Tinamous/ReallySmartBox/Images/2017-08-14 11.56.22.jpg

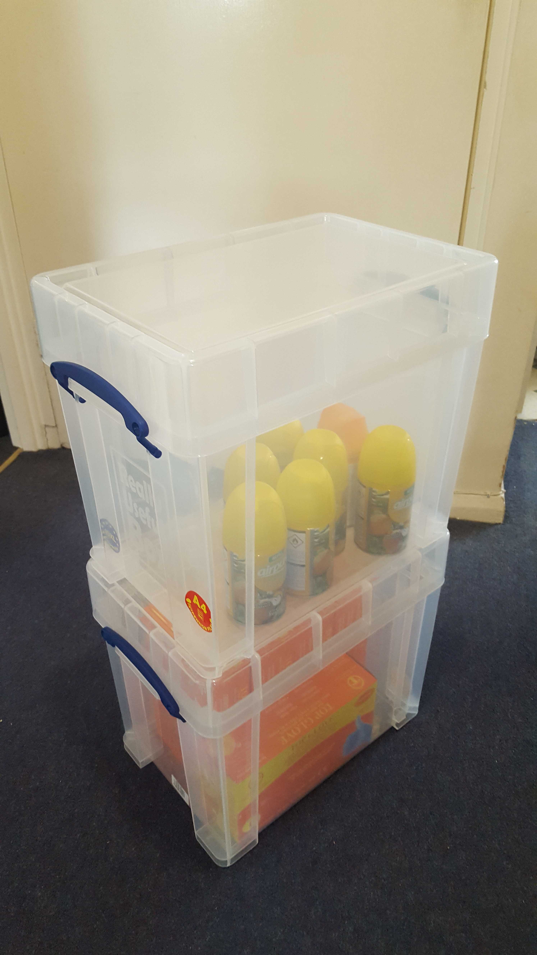
Images/2017-08-14 11.56.22.jpg
