Tinamous/ReallySmartBox/Images/2017-08-14 11.56.32.jpg

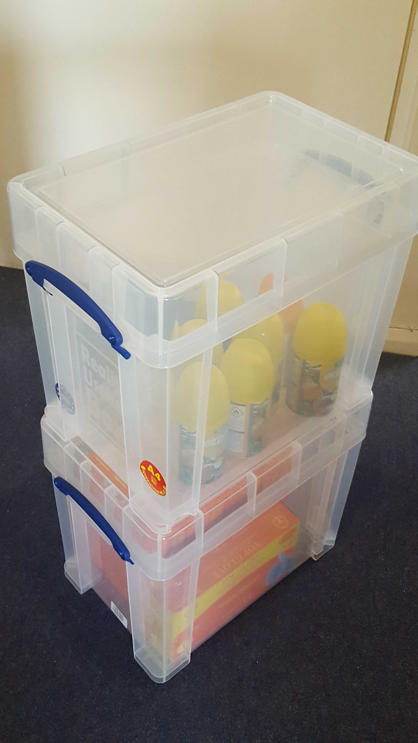
Images/2017-08-14 11.56.32.jpg
