Tinamous/ReallySmartBox/Images/2017-08-14 11.58.28.jpg

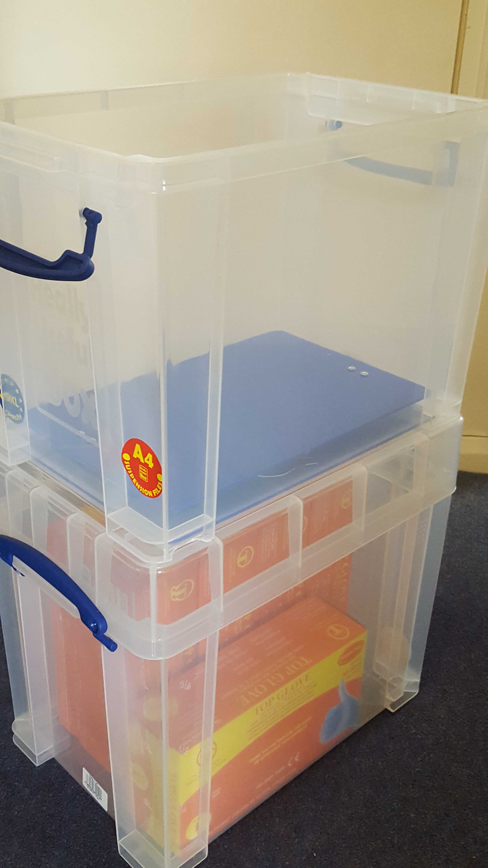
Images/2017-08-14 11.58.28.jpg
