Tinamous/ReallySmartBox/Images/2017-08-14 11.59.04.jpg

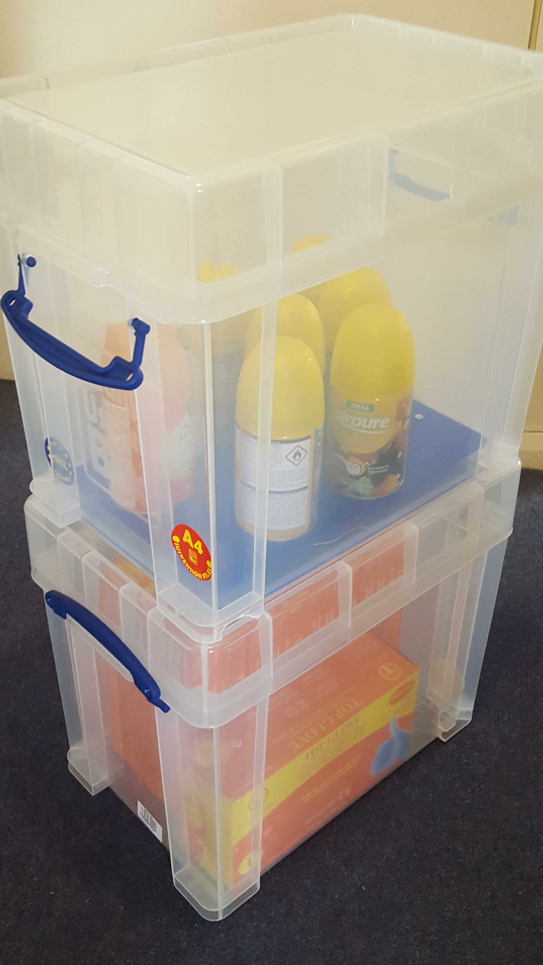
Images/2017-08-14 11.59.04.jpg
