Tinamous/ReallySmartBox/Images/2017-08-14 12.00.39.jpg

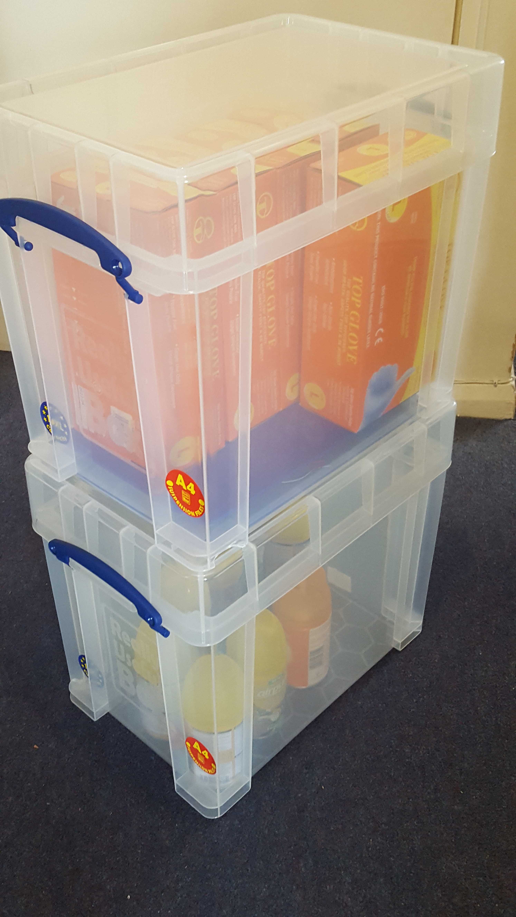
Images/2017-08-14 12.00.39.jpg
