Tinamous/ReallySmartBox/Images/2017-08-14 12.01.01.jpg

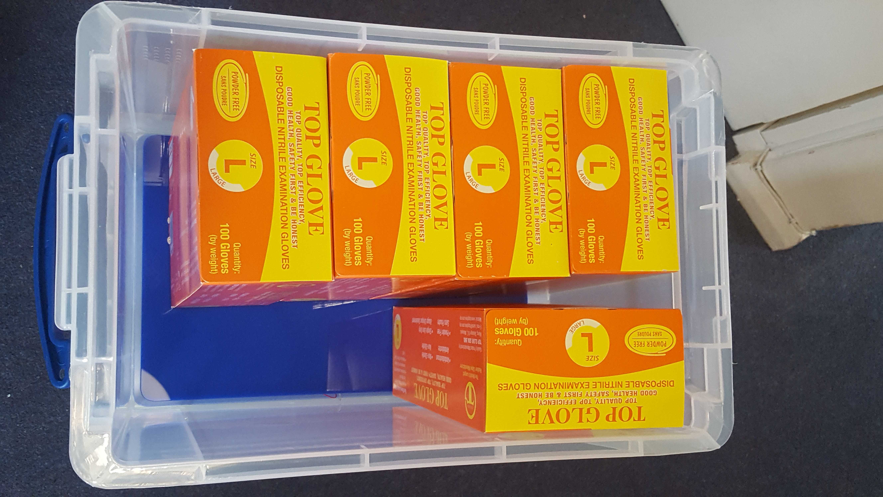
Images/2017-08-14 12.01.01.jpg
