Tinamous/ReallySmartBox/Images/2017-08-14 13.37.10.jpg

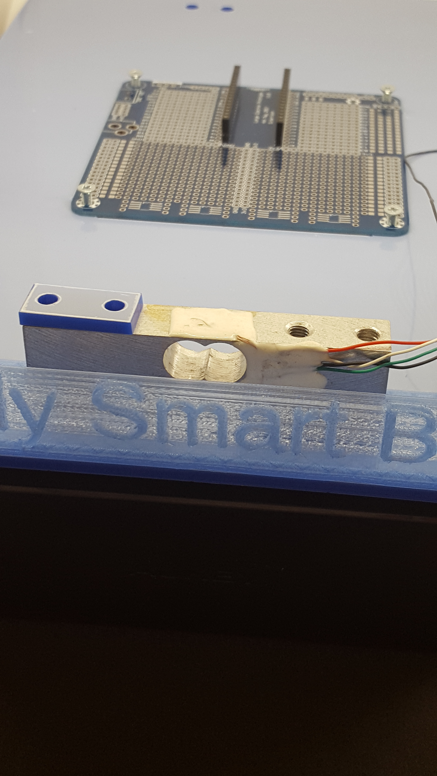
Images/2017-08-14 13.37.10.jpg
