Tinamous/ReallySmartBox/Images/2017-08-14 13.40.55.jpg

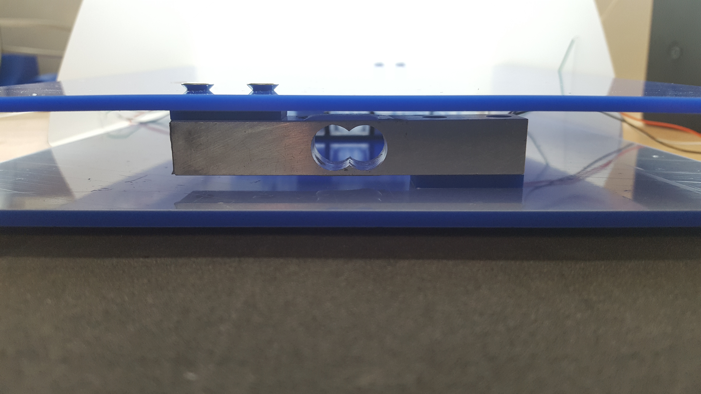
Images/2017-08-14 13.40.55.jpg
