Tinamous/ReallySmartBox/Images/2017-08-14 13.41.03.jpg

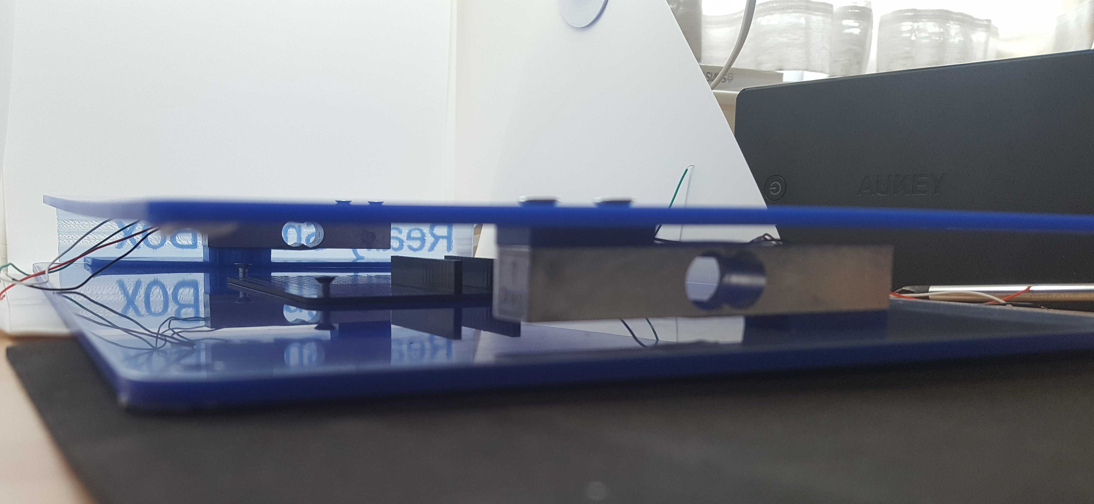
Images/2017-08-14 13.41.03.jpg
