Tinamous/ReallySmartBox/Images/2017-11-07 12.58.53.jpg

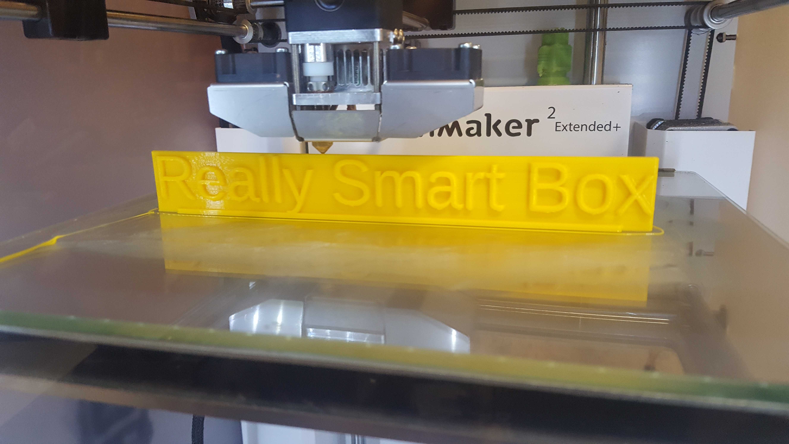
Images/2017-11-07 12.58.53.jpg
