Tinamous/ReallySmartBox/Images/2017-11-07 18.37.57.jpg

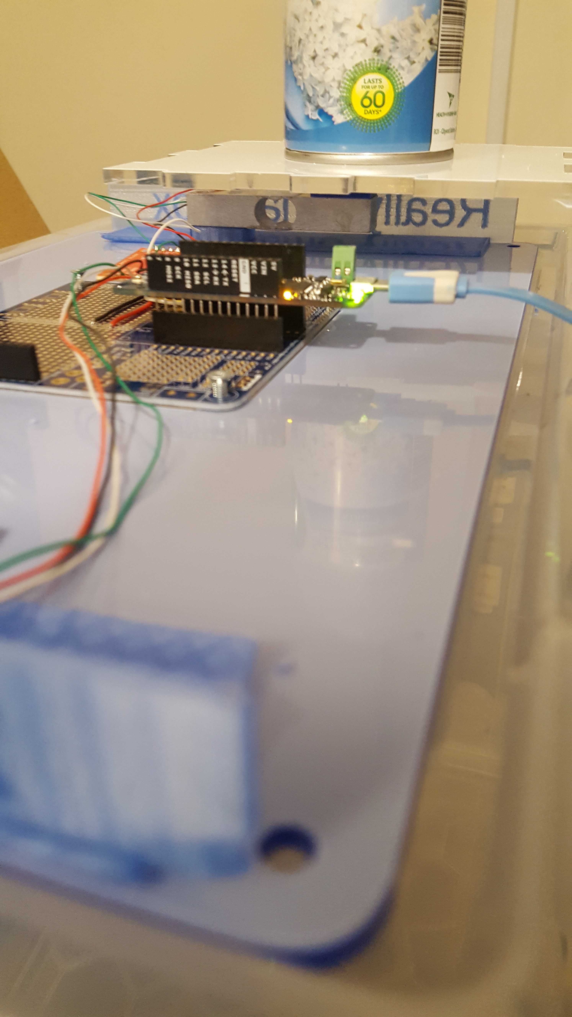
Images/2017-11-07 18.37.57.jpg
