Tinamous/ReallySmartBox/Images/2017-11-07 18.38.00.jpg

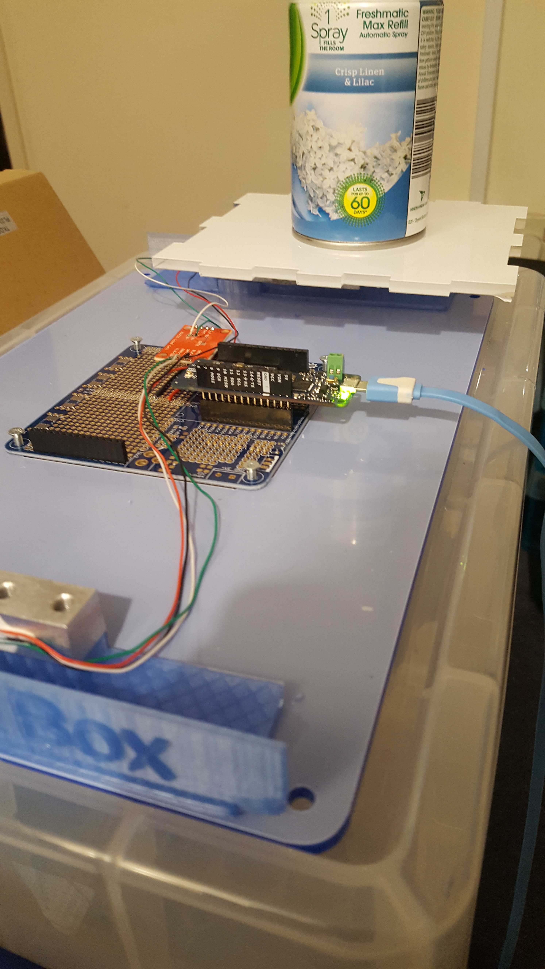
Images/2017-11-07 18.38.00.jpg
