Tinamous/ReallySmartBox/Images/2017-11-08 00.15.52.jpg

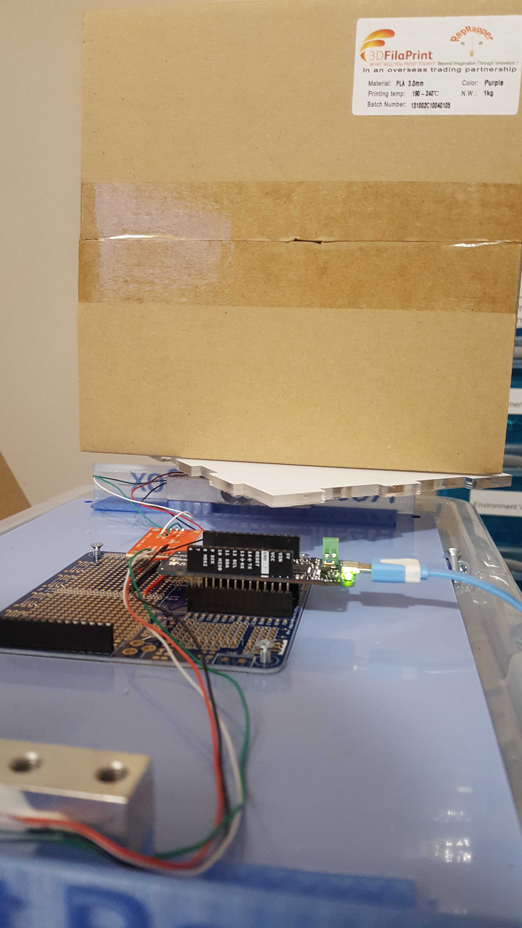
Images/2017-11-08 00.15.52.jpg
