Tinamous/ReallySmartBox/Images/2017-11-08 05.06.58.jpg

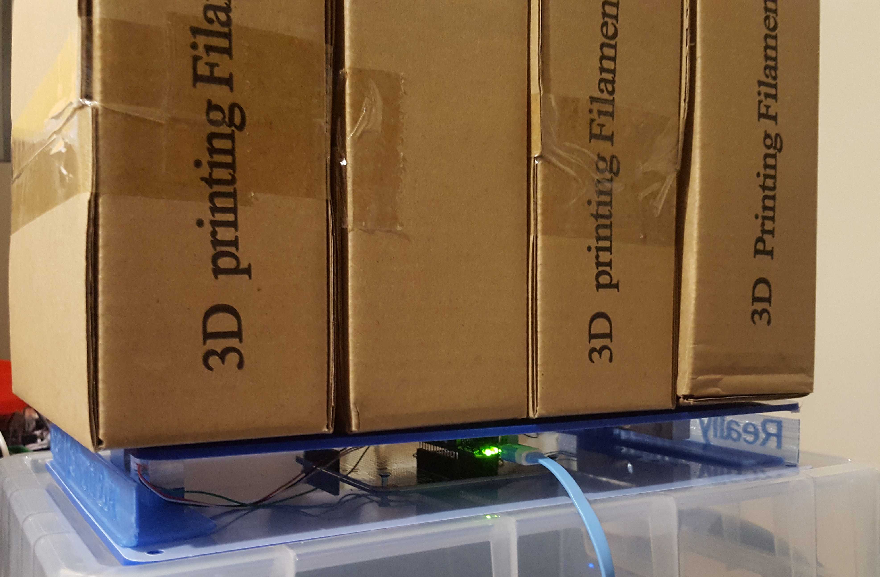
Images/2017-11-08 05.06.58.jpg
