Tinamous/ReallySmartBox/Images/2017-11-09 22.32.21.jpg

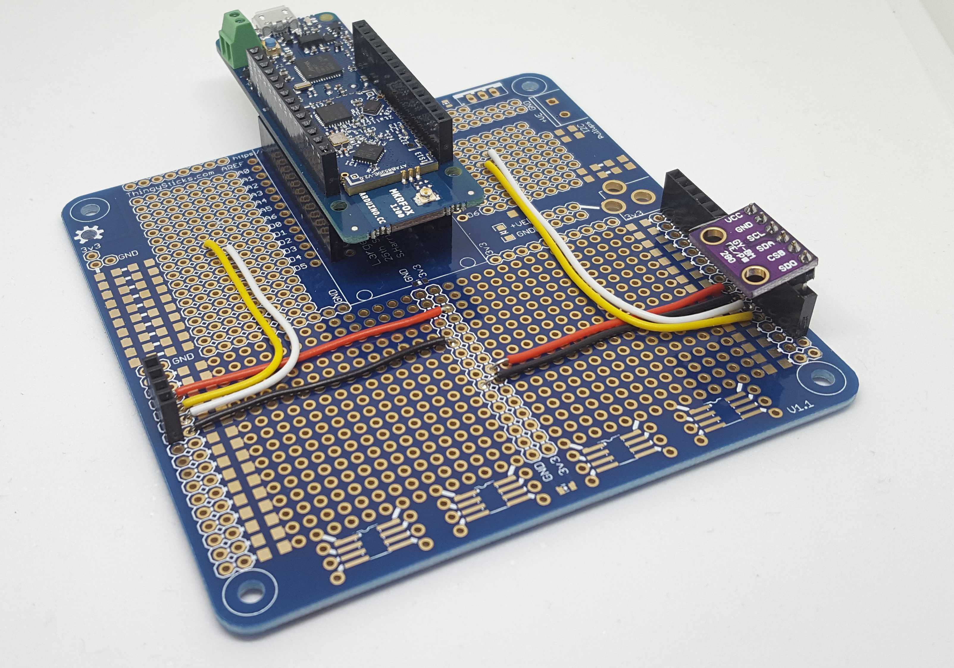
Images/2017-11-09 22.32.21.jpg
