Tinamous/ReallySmartBox/Images/2017-11-09 22.32.29.jpg

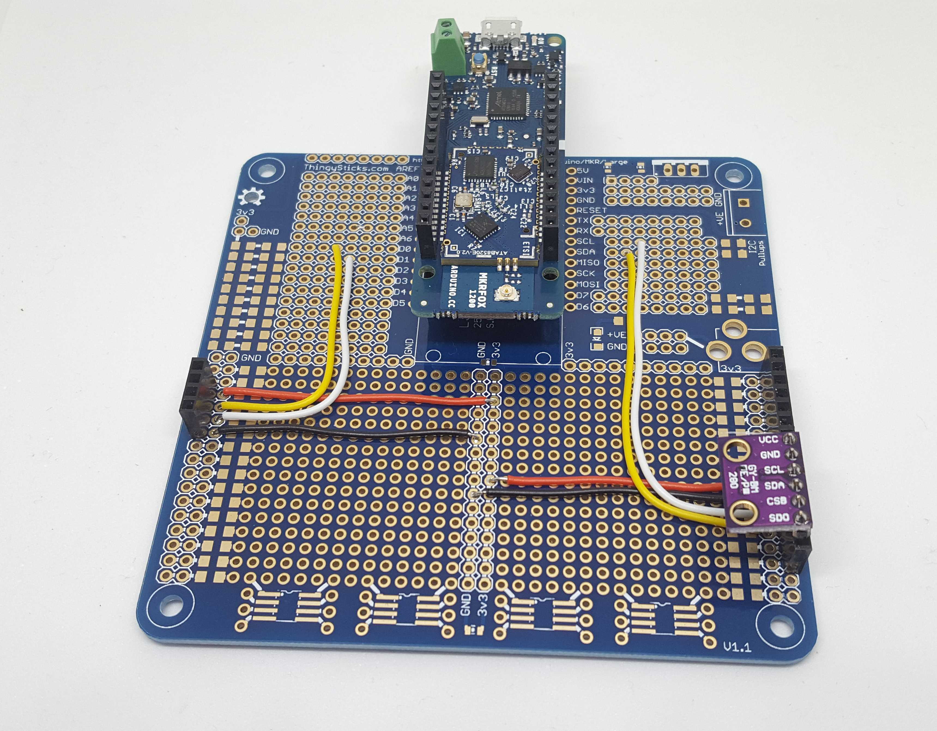
Images/2017-11-09 22.32.29.jpg
