Tinamous/ReallySmartBox/Images/2017-11-10 00.08.54.jpg

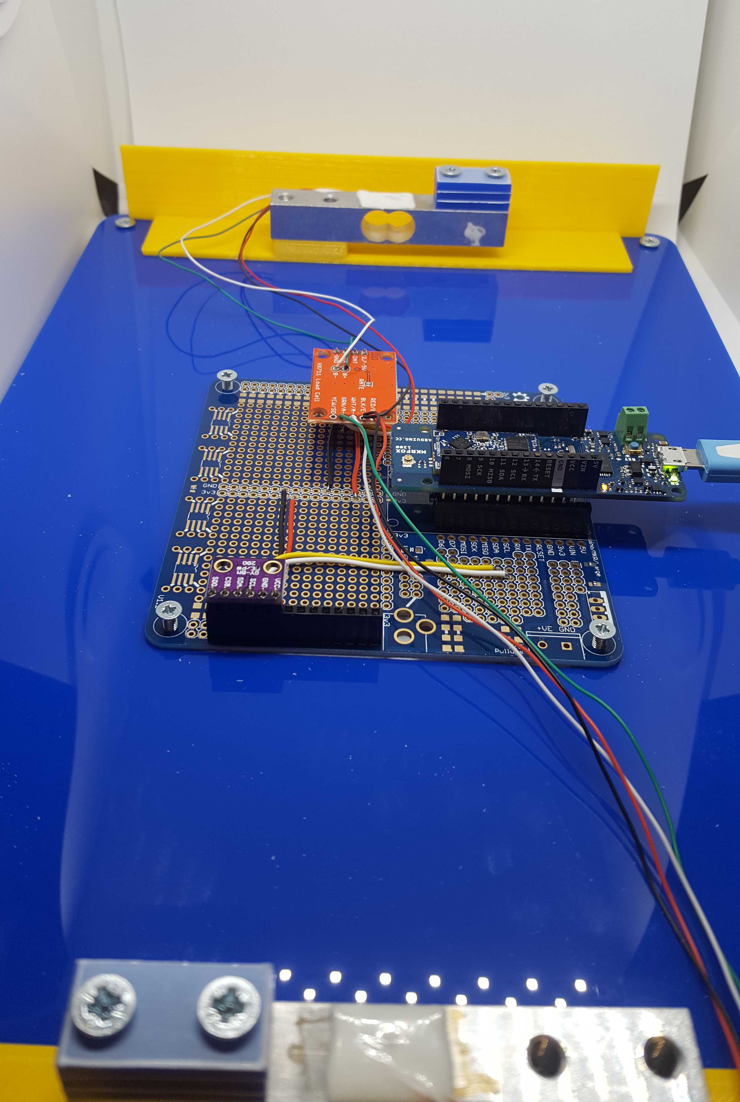
Images/2017-11-10 00.08.54.jpg
