Tinamous/ReallySmartBox/Images/2017-11-10 00.09.11.jpg

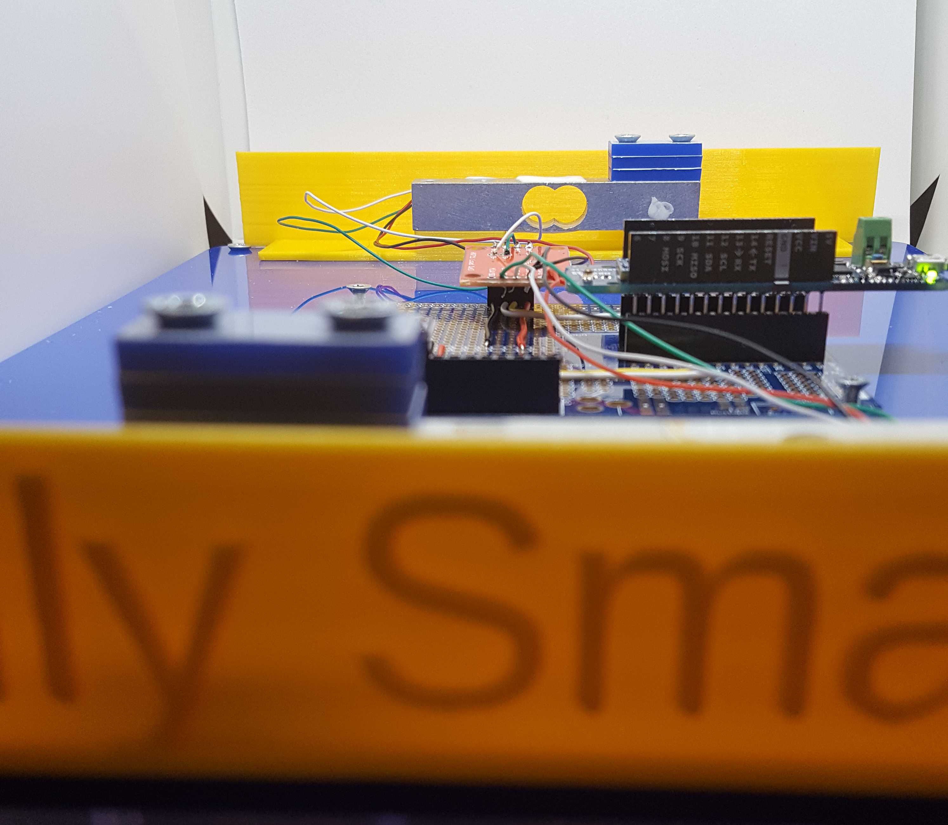
Images/2017-11-10 00.09.11.jpg
