Tinamous/ReallySmartBox/Images/2017-11-10 00.32.09.jpg

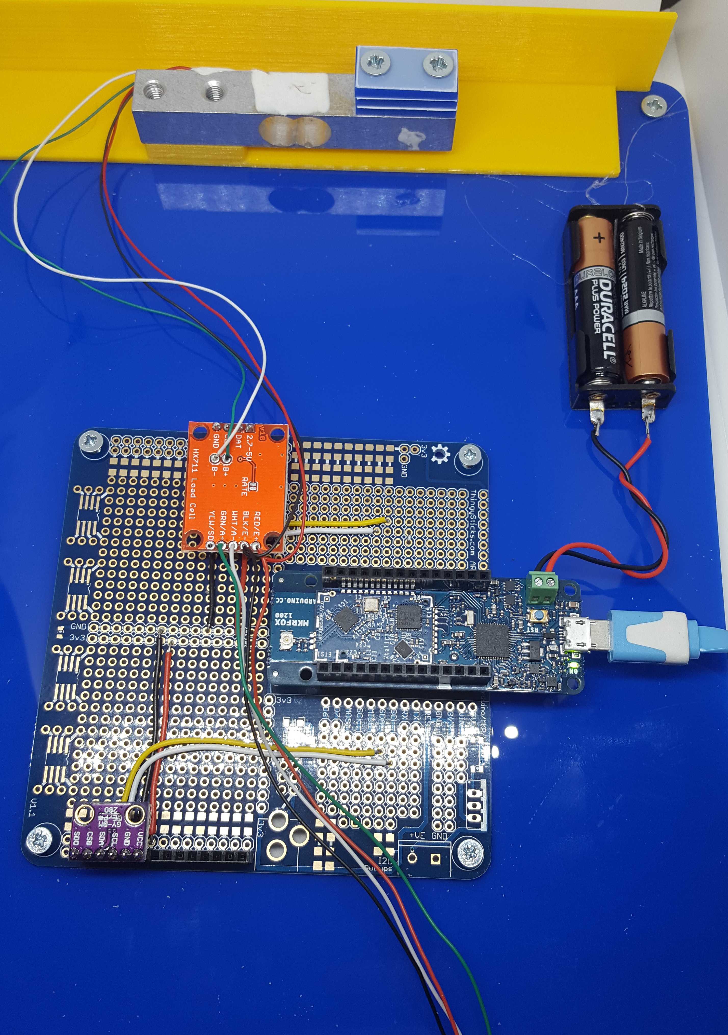
Images/2017-11-10 00.32.09.jpg
