Tinamous/ReallySmartBox/Images/2017-11-10 12.50.05.jpg

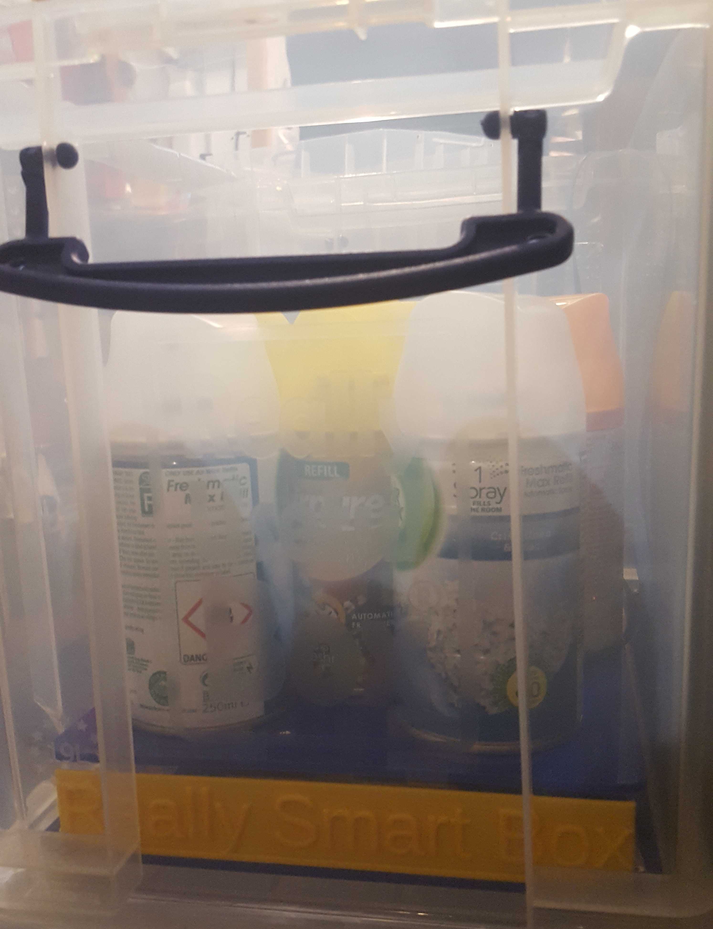
Images/2017-11-10 12.50.05.jpg
