Tinamous/ReallySmartBox/Images/2017-11-10 12.57.34.jpg

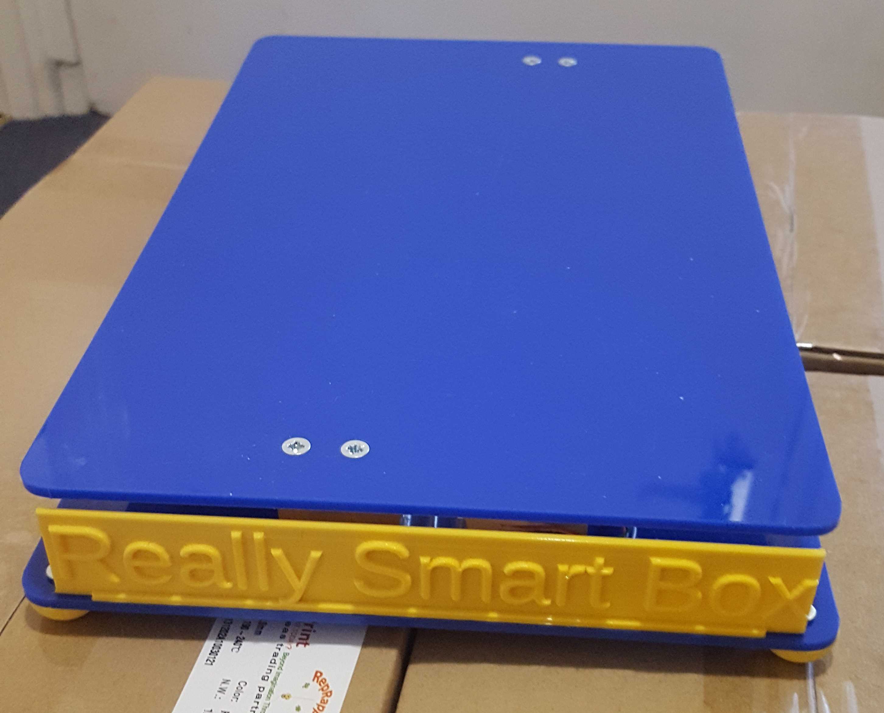
Images/2017-11-10 12.57.34.jpg
