Tinamous/ReallySmartBox/Images/2017-11-10 12.58.54.jpg

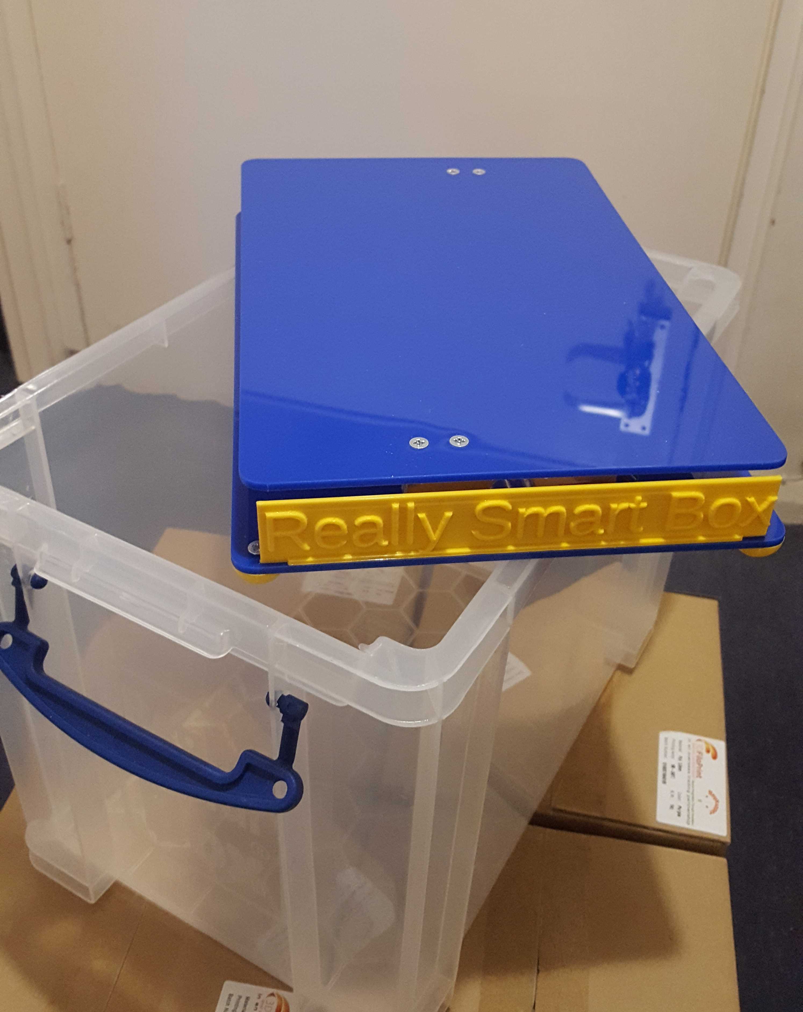
Images/2017-11-10 12.58.54.jpg
