Tinamous/ReallySmartBox/Images/2017-11-10 13.21.07.jpg

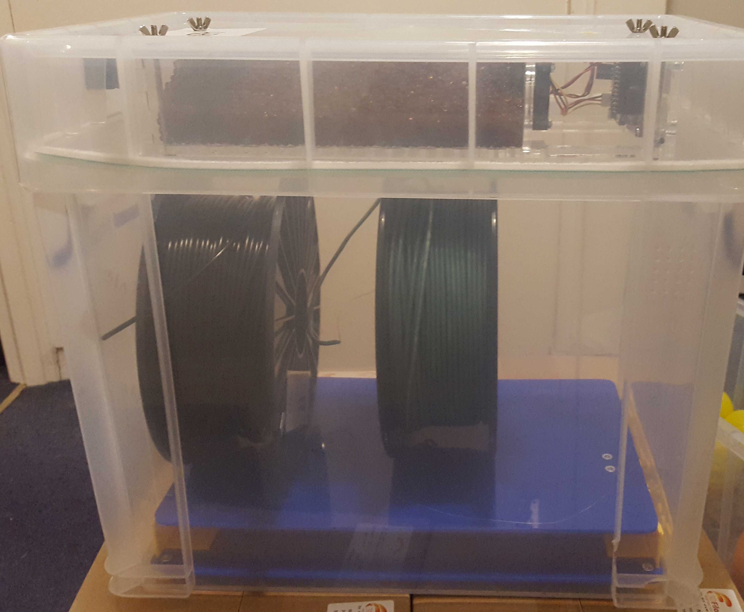
Images/2017-11-10 13.21.07.jpg
