Tinamous/ReallySmartBox/Images/2017-11-10 13.21.45.jpg

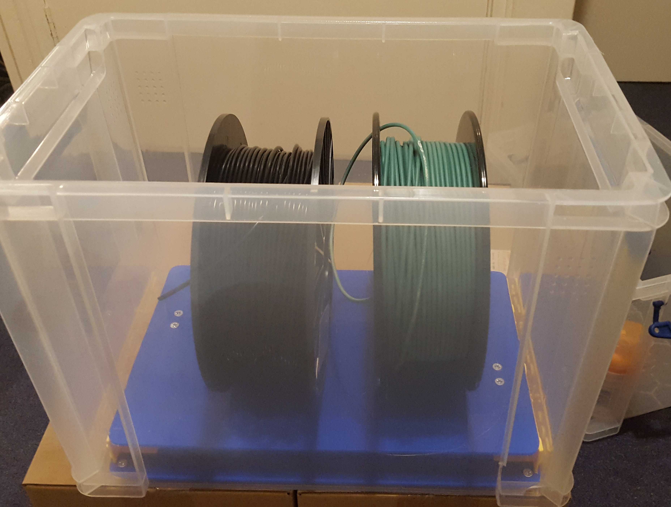
Images/2017-11-10 13.21.45.jpg
