Tinamous/ReallySmartBox/Images/Ack.jpg

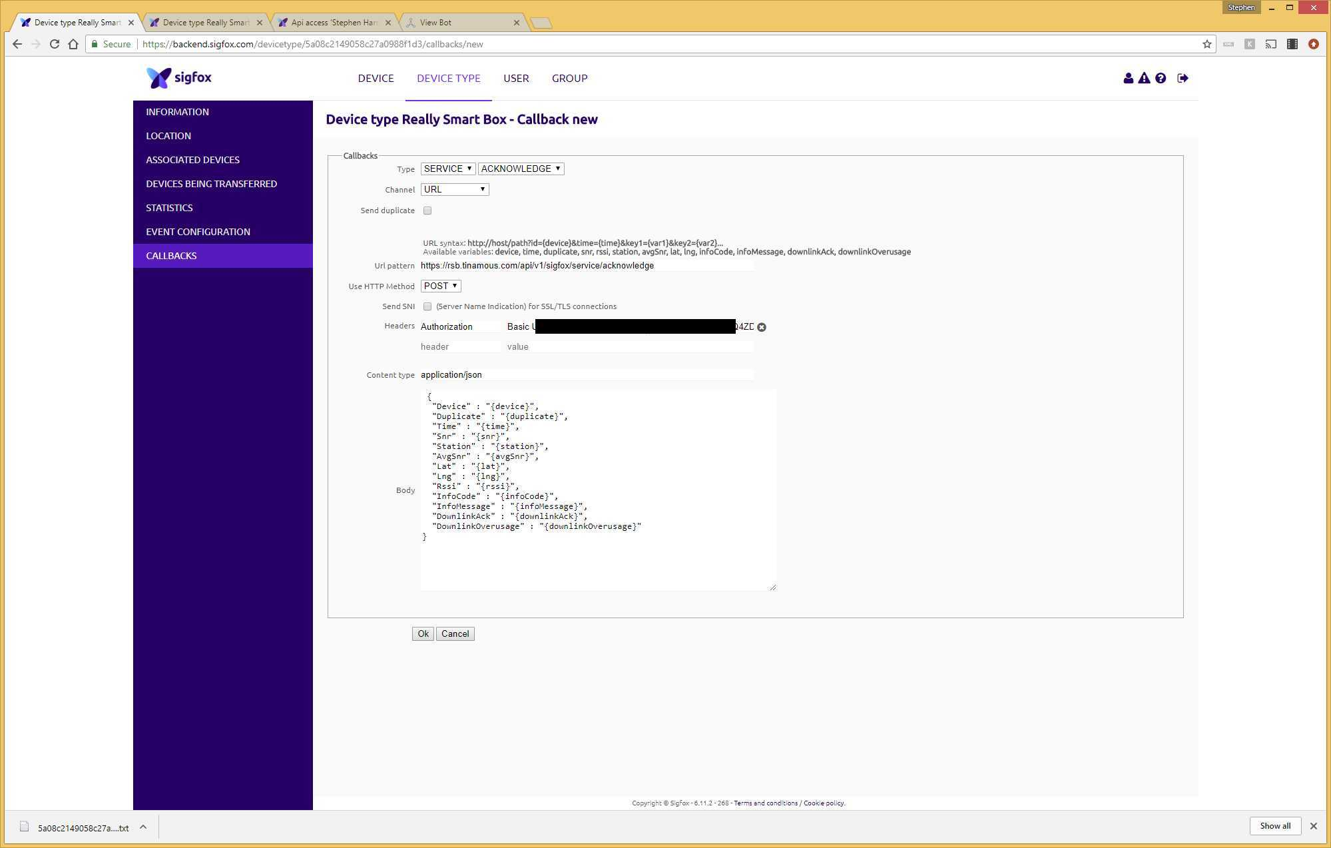
Images/Ack.jpg
