Tinamous/ReallySmartBox/Images/Activation1.jpg

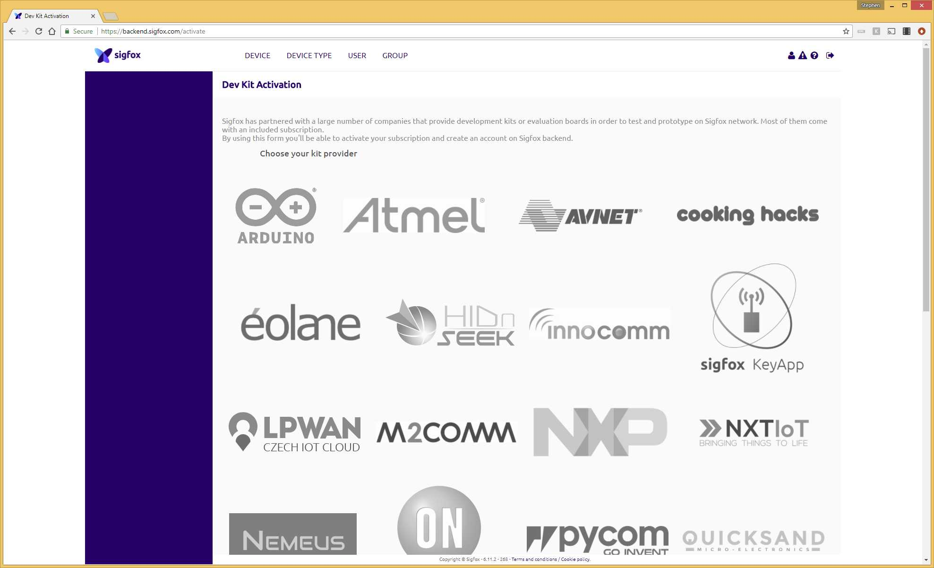
Images/Activation1.jpg
