Tinamous/ReallySmartBox/Images/Activation2.jpg

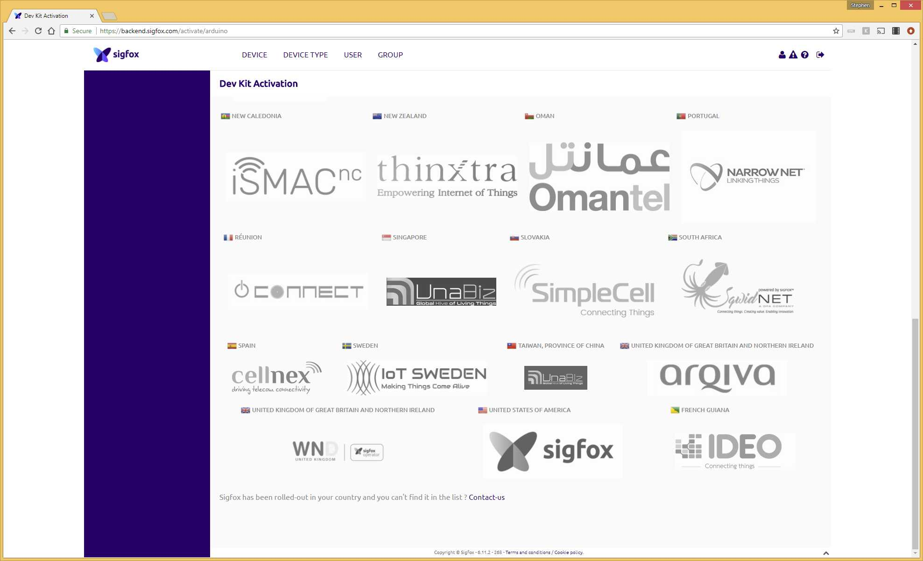
Images/Activation2.jpg
