Tinamous/ReallySmartBox/Images/Activation3.jpg

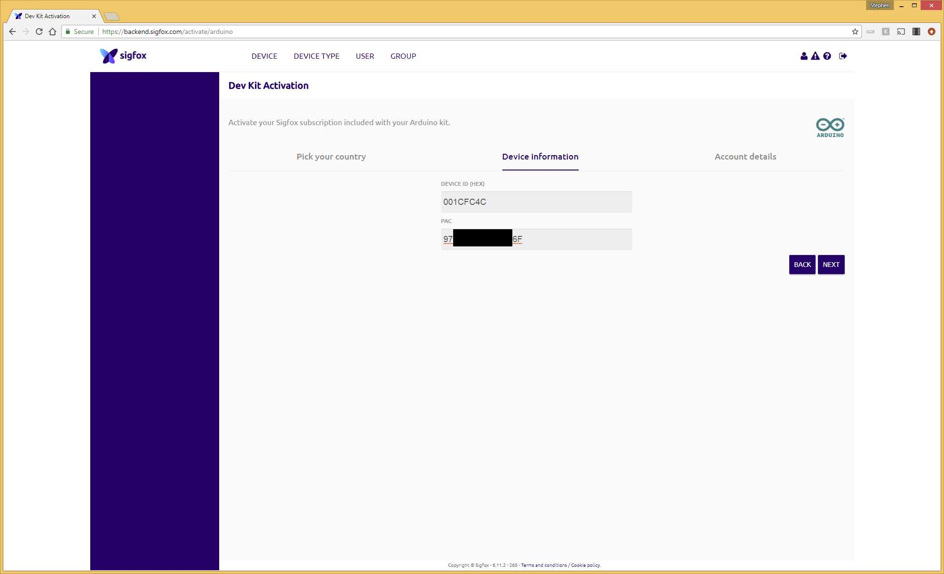
Images/Activation3.jpg
