Tinamous/ReallySmartBox/Images/Activation5.jpg

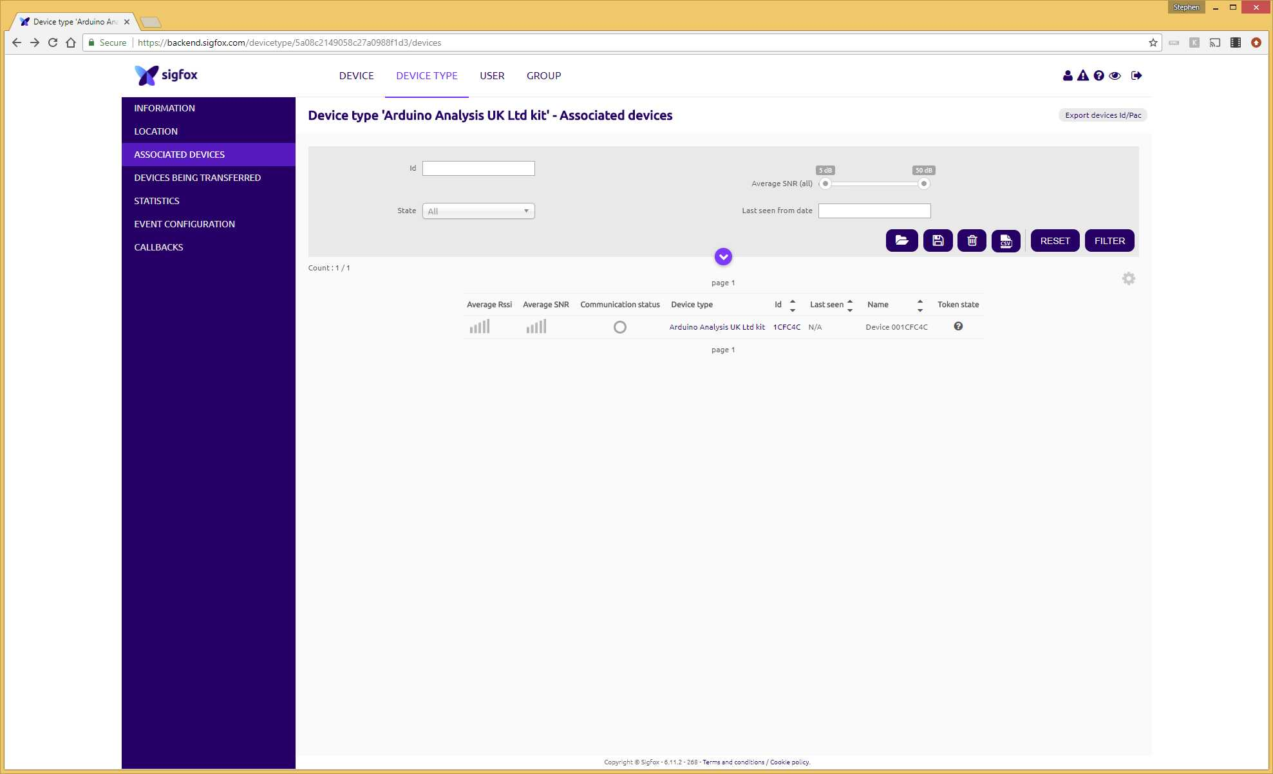
Images/Activation5.jpg
