Tinamous/ReallySmartBox/Images/Callback1.jpg

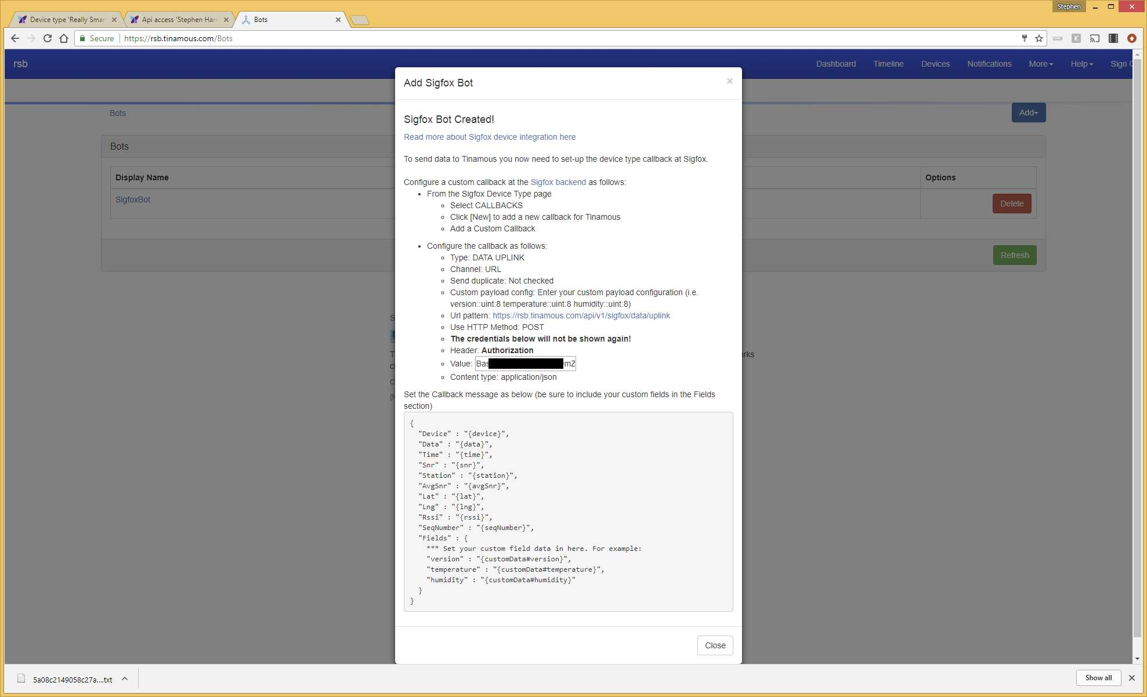
Images/Callback1.jpg
