Tinamous/ReallySmartBox/Images/Callback3.jpg

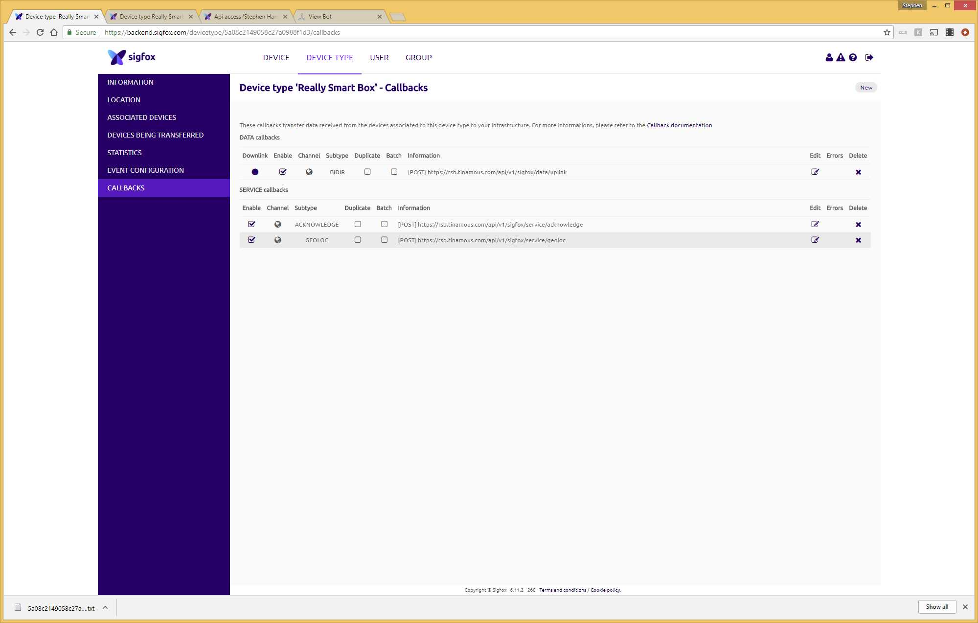
Images/Callback3.jpg
