Tinamous/ReallySmartBox/Images/Dashboard-1.jpg

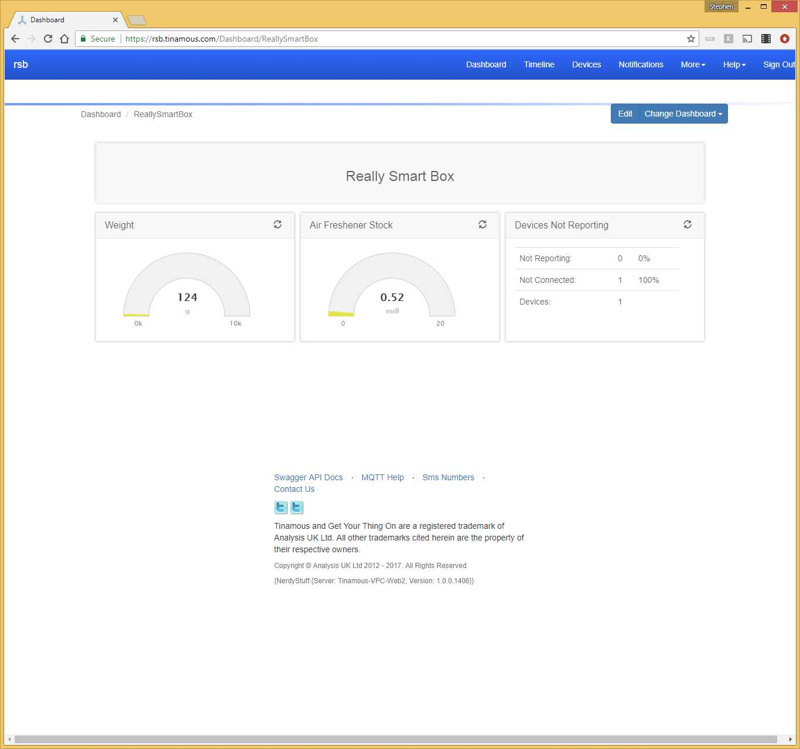
Images/Dashboard-1.jpg
