Tinamous/ReallySmartBox/Images/Dashboard-2.jpg

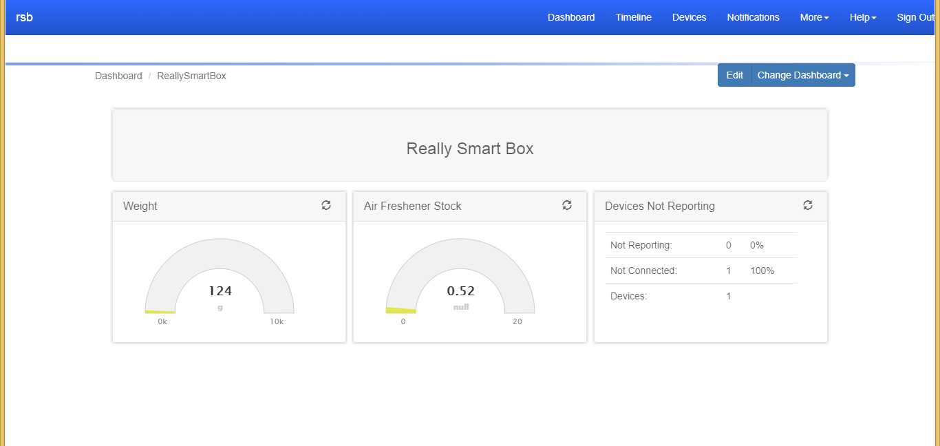
Images/Dashboard-2.jpg
