Tinamous/ReallySmartBox/Images/Device1.jpg

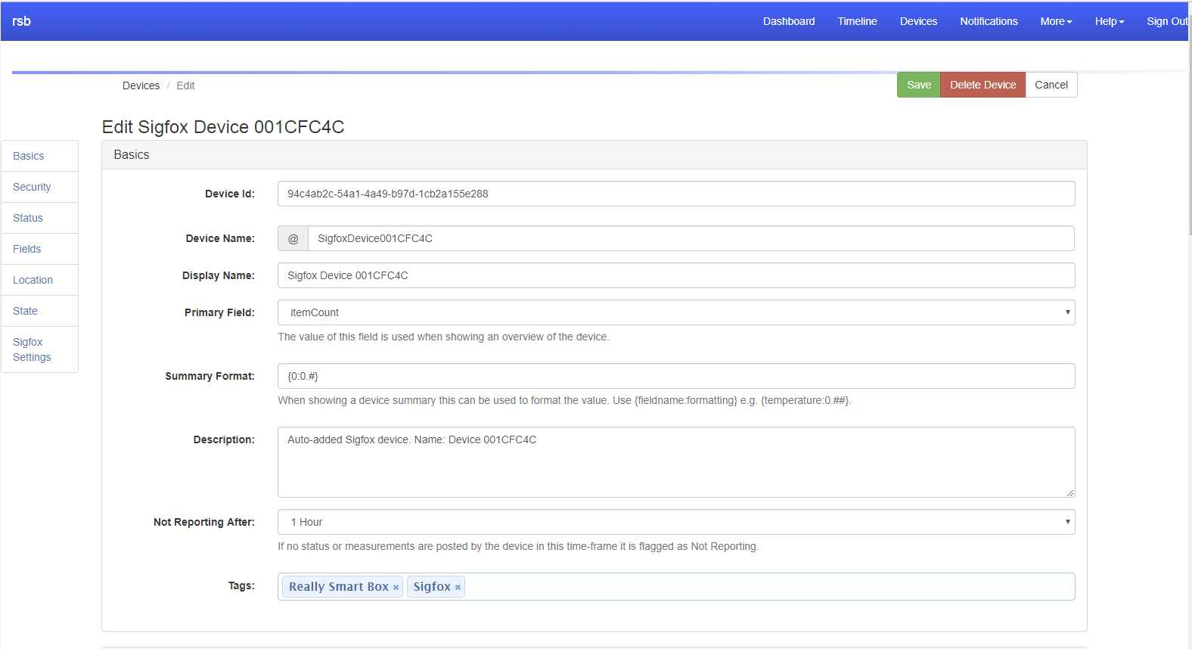
Images/Device1.jpg
