Tinamous/ReallySmartBox/Images/Device2.jpg

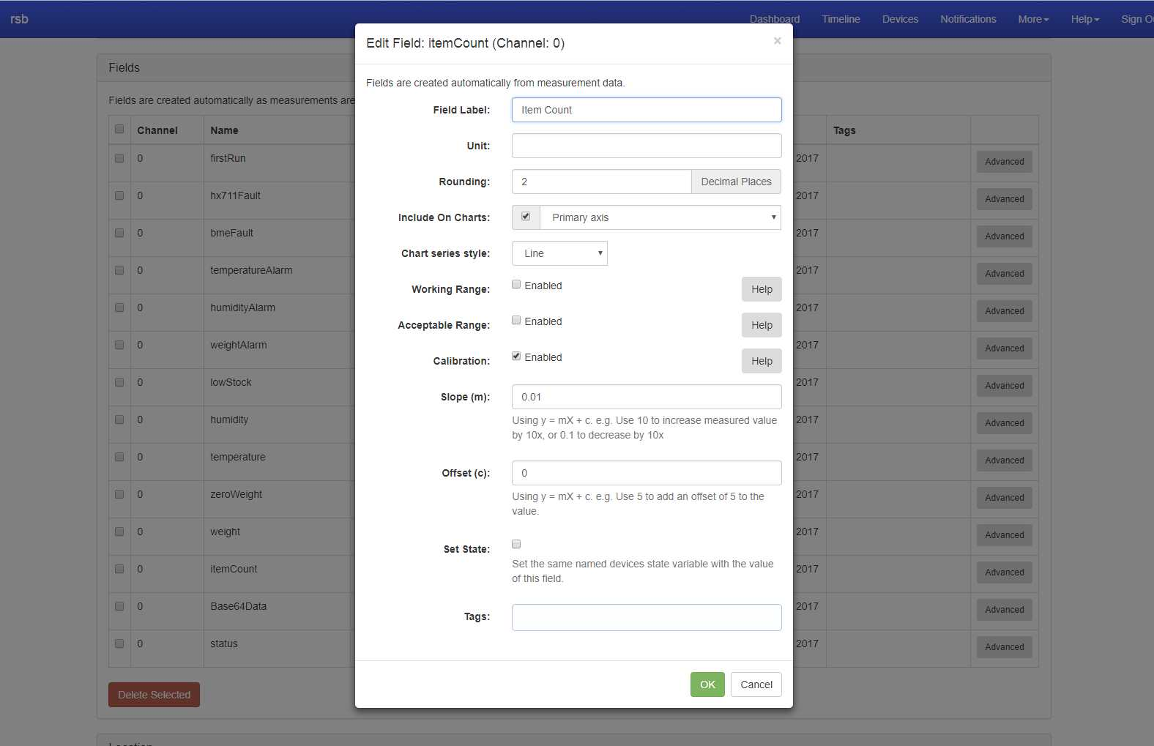
Images/Device2.jpg
