Tinamous/ReallySmartBox/Images/Device3.jpg

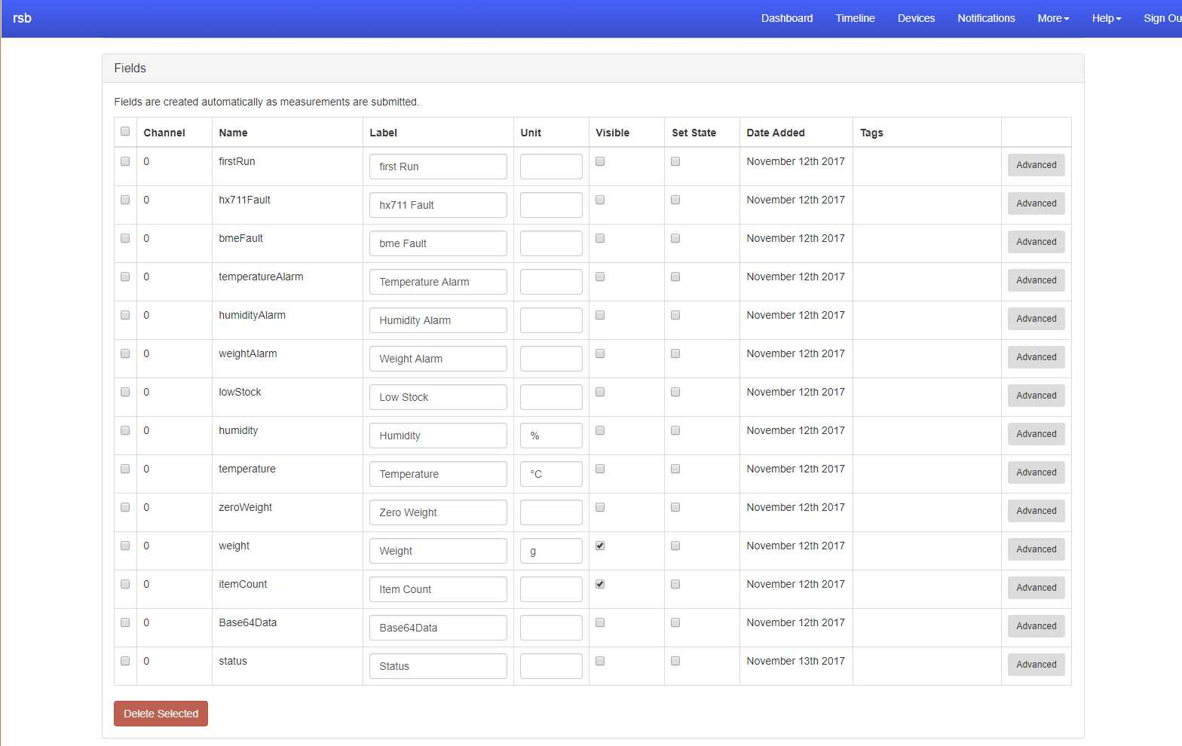
Images/Device3.jpg
