Tinamous/ReallySmartBox/Images/Device4.jpg

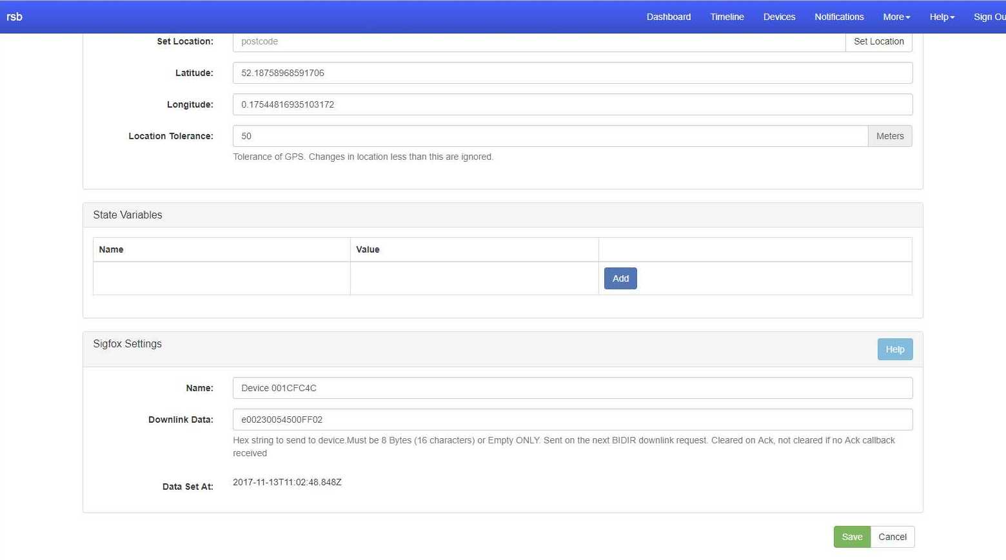
Images/Device4.jpg
