Tinamous/ReallySmartBox/Images/Device-SigfoxDetails2.jpg

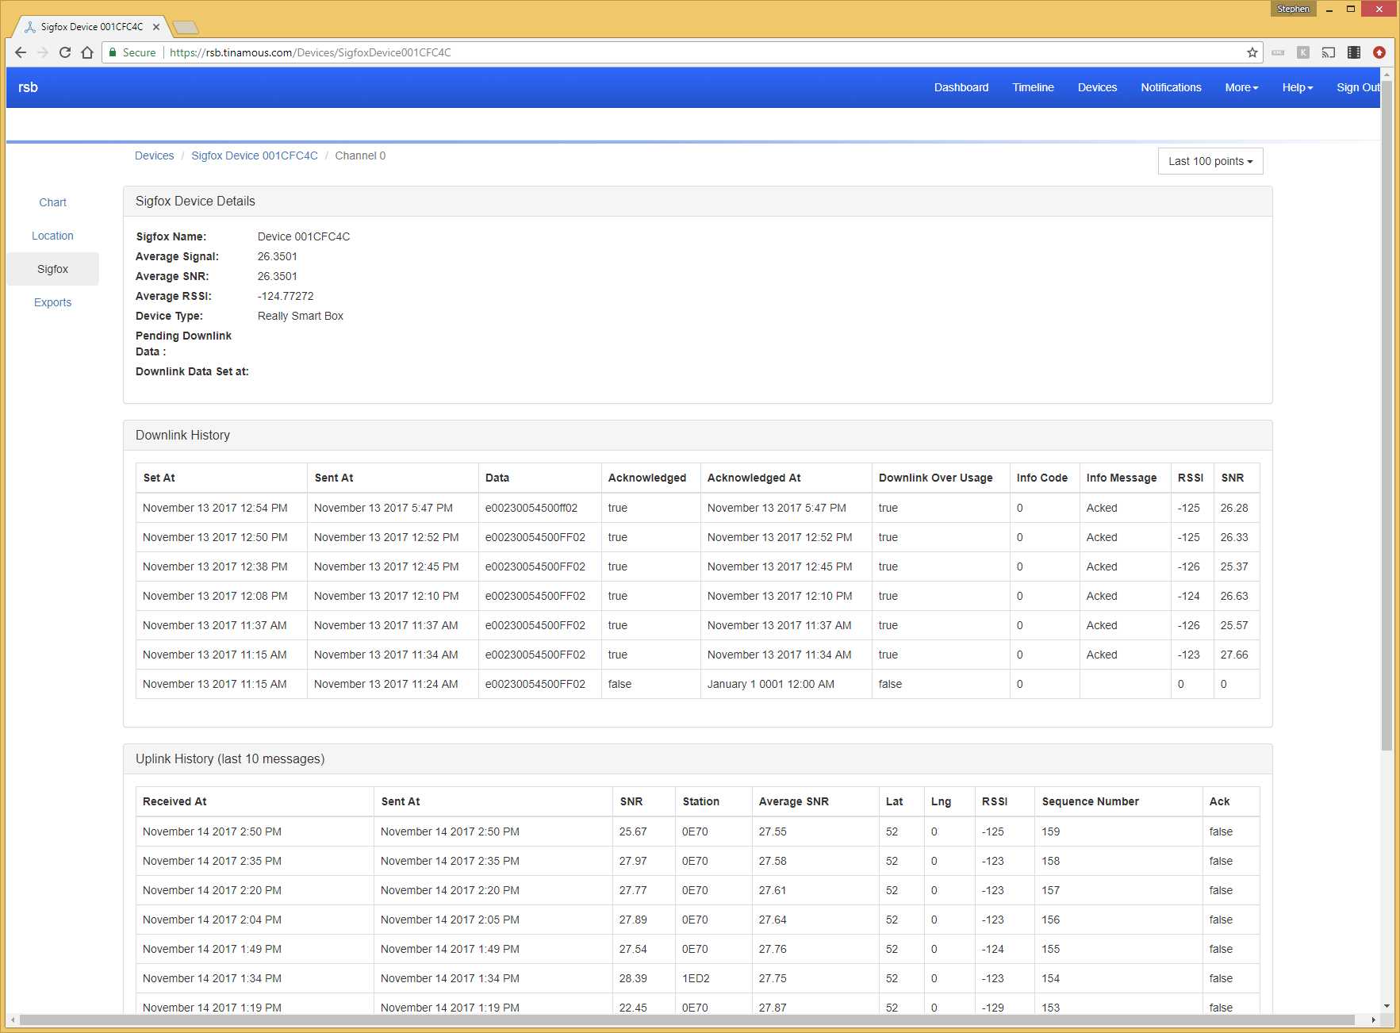
Images/Device-SigfoxDetails2.jpg
