Tinamous/ReallySmartBox/Images/Device-SigfoxDetails.jpg

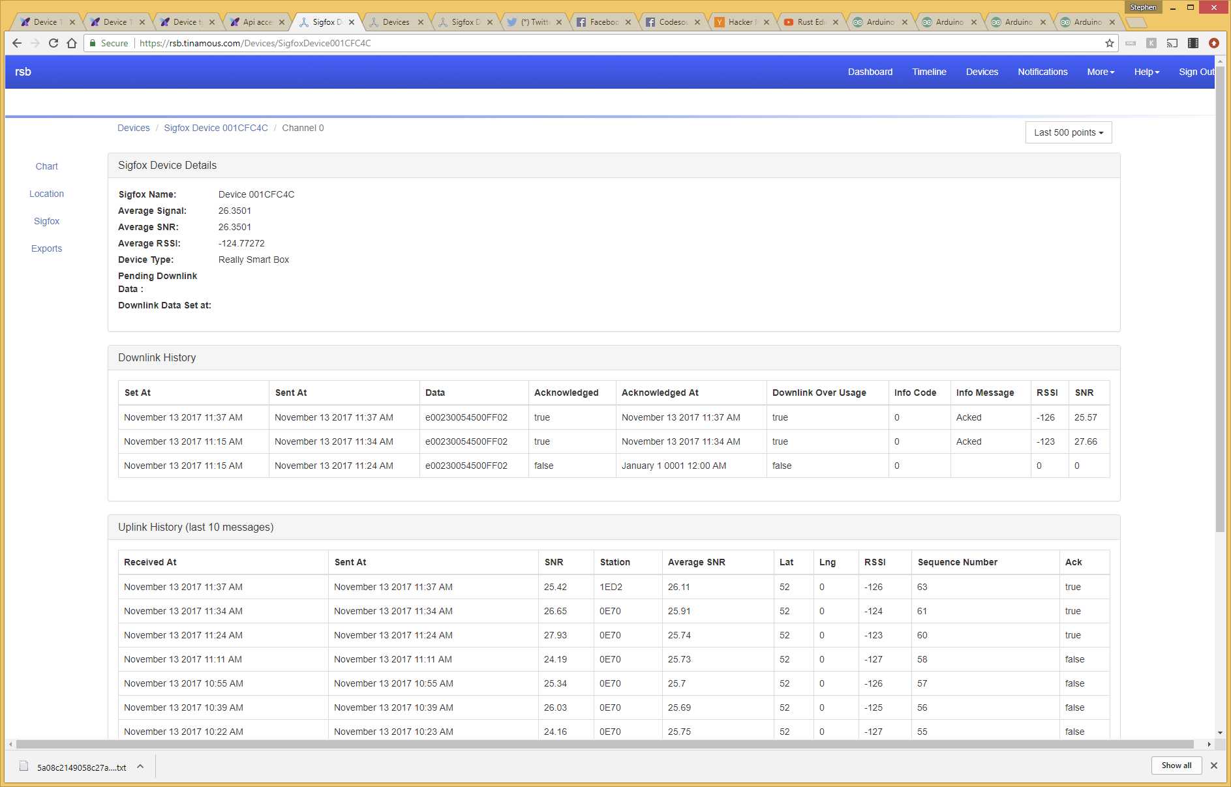
Images/Device-SigfoxDetails.jpg
