Tinamous/ReallySmartBox/Images/DeviceDetails.jpg

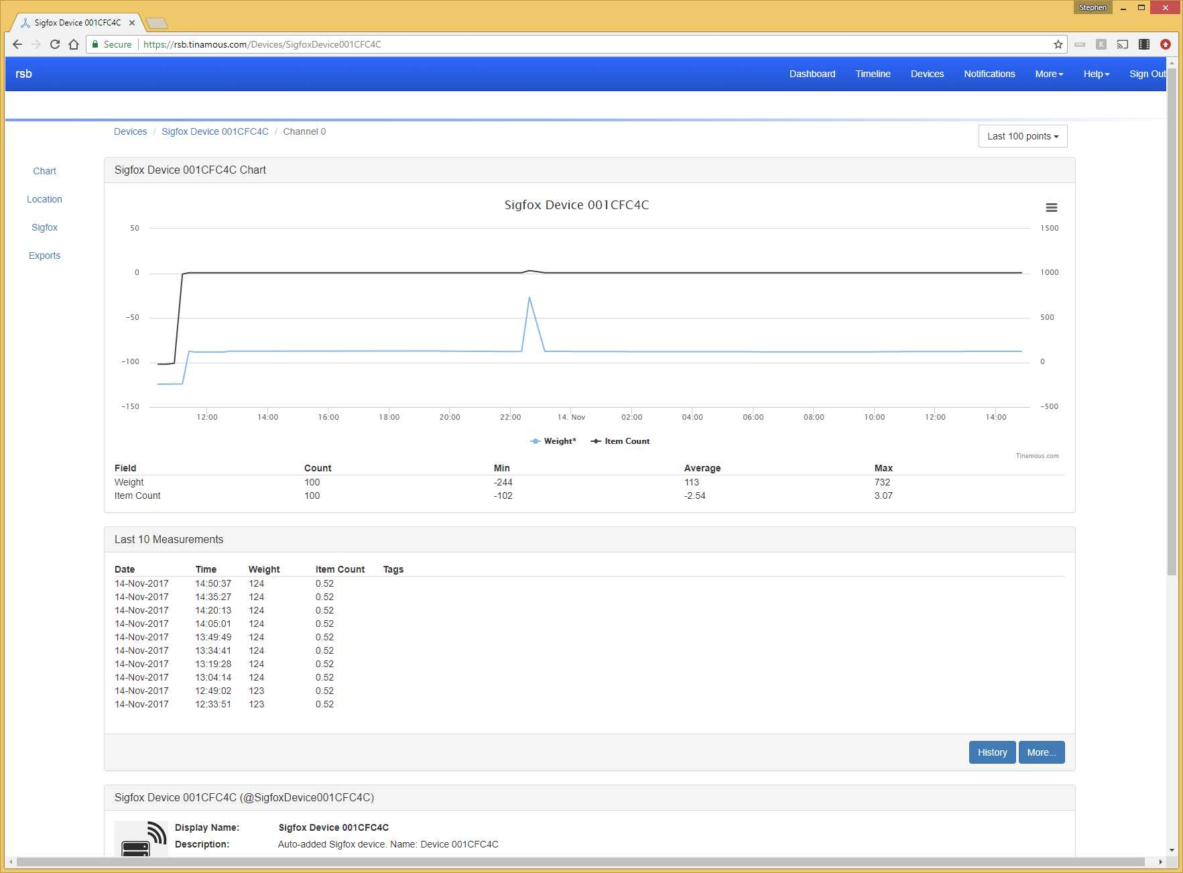
Images/DeviceDetails.jpg
