Tinamous/ReallySmartBox/Images/DeviceLimits.jpg

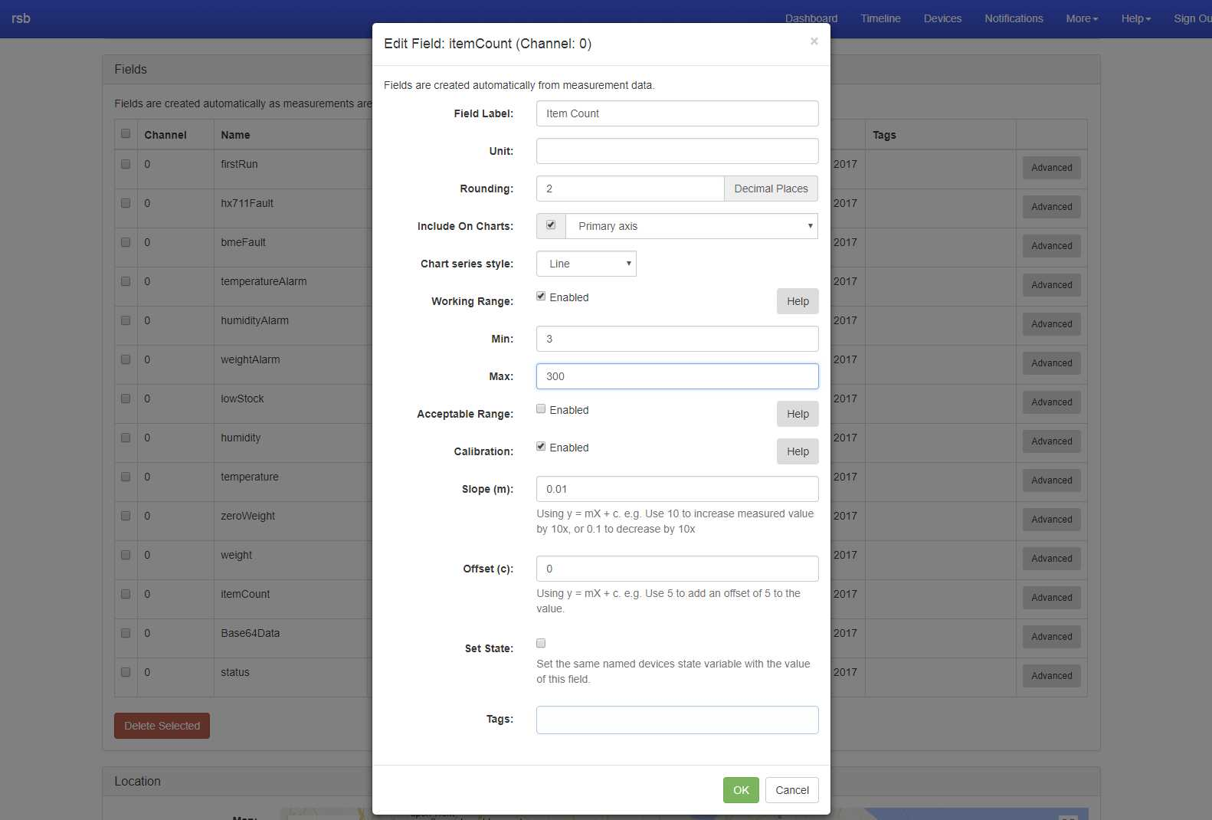
Images/DeviceLimits.jpg
