Tinamous/ReallySmartBox/Images/DownlinkCallback.jpg

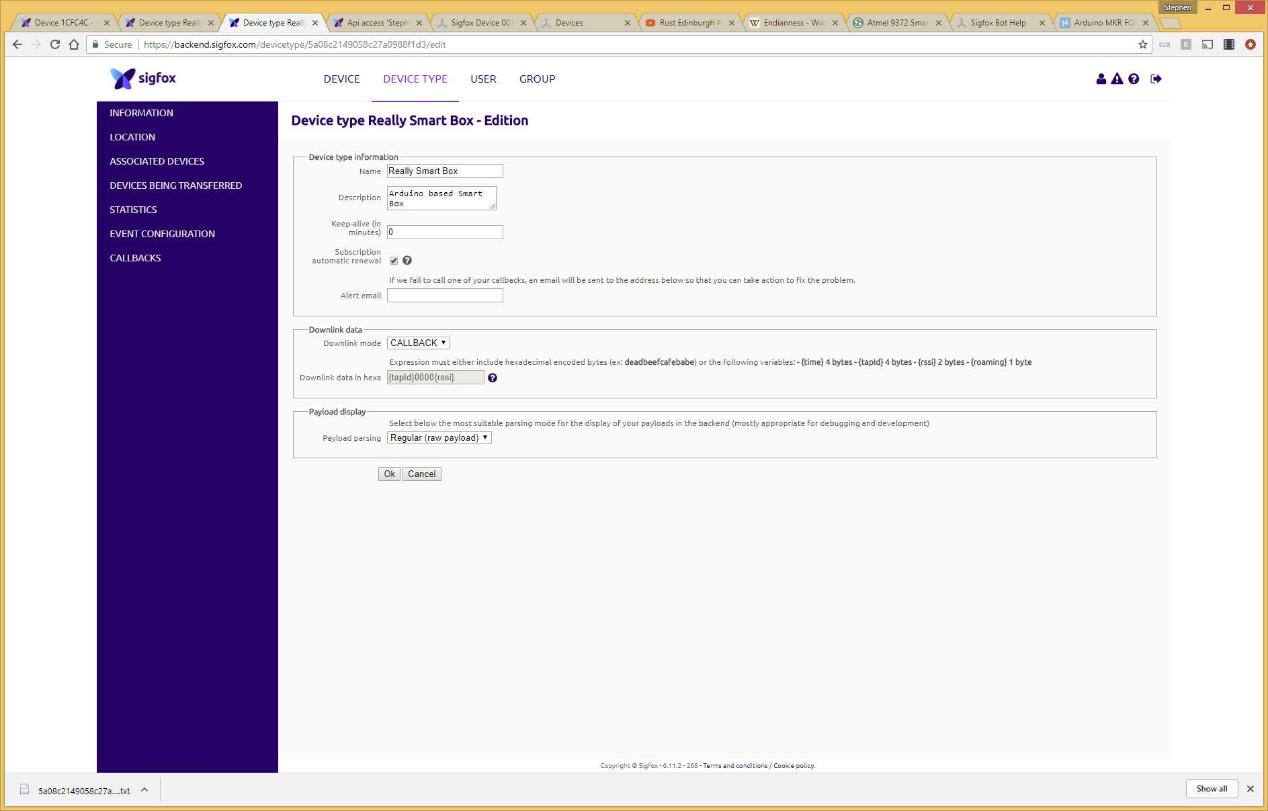
Images/DownlinkCallback.jpg
