Tinamous/ReallySmartBox/Images/ElectornicsFitted.jpg

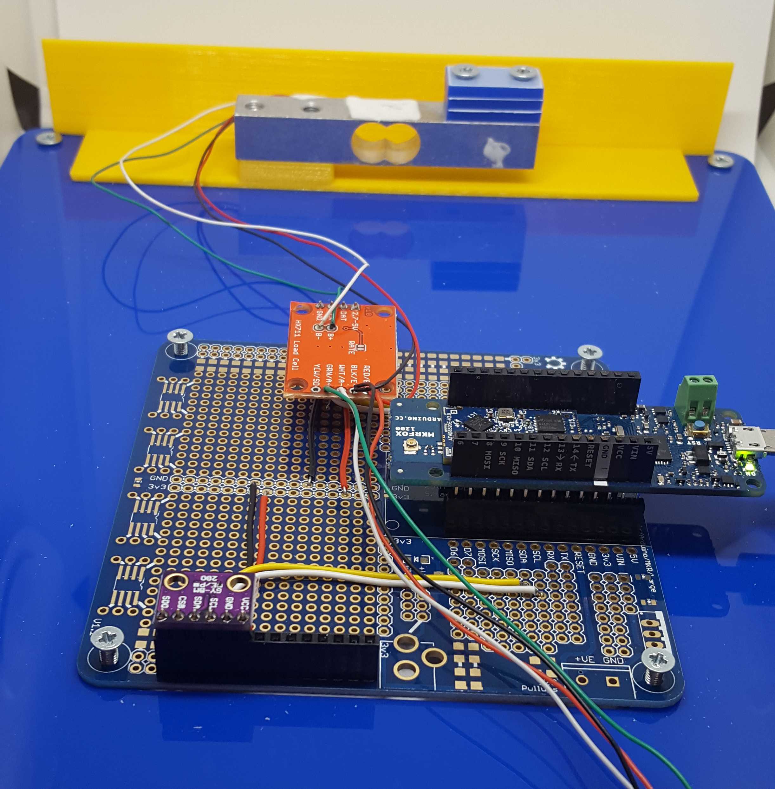
Images/ElectornicsFitted.jpg
