Tinamous/ReallySmartBox/Images/FilamentStorage.jpg

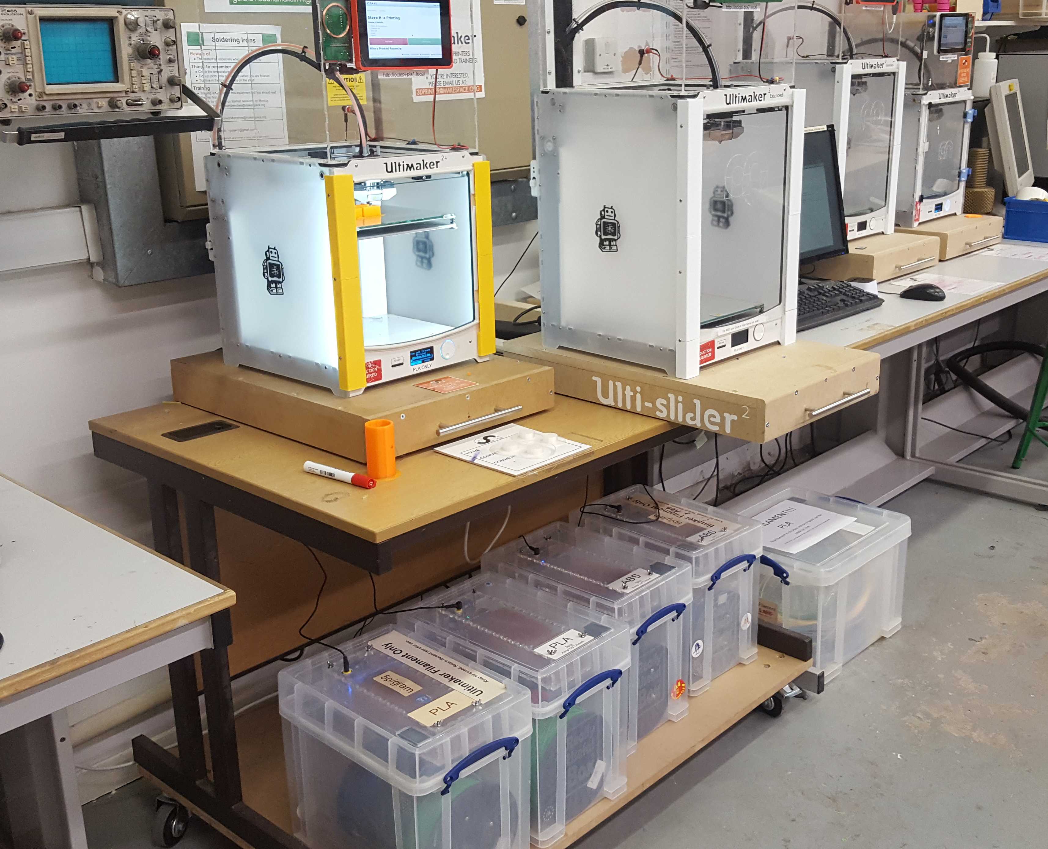
Images/FilamentStorage.jpg
