Tinamous/ReallySmartBox/Images/GeoLoc.jpg

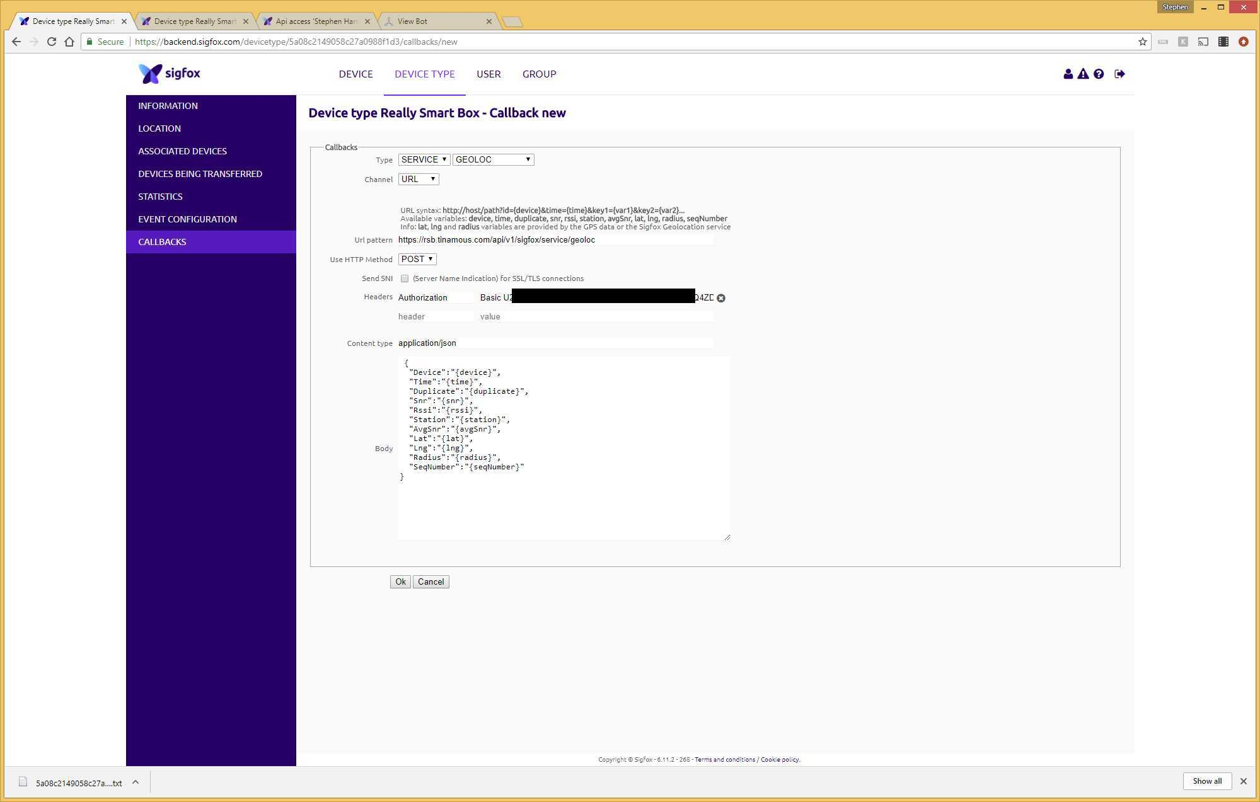
Images/GeoLoc.jpg
