Tinamous/ReallySmartBox/Images/HX711.jpg

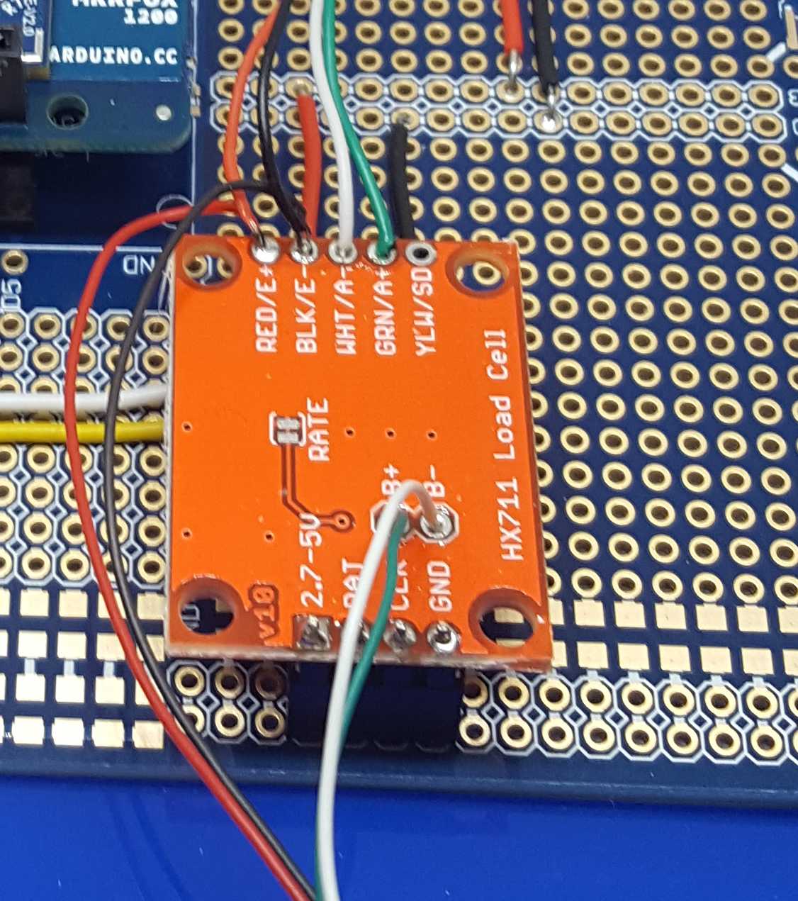
Images/HX711.jpg
