Tinamous/ReallySmartBox/Images/LoadCell.jpg

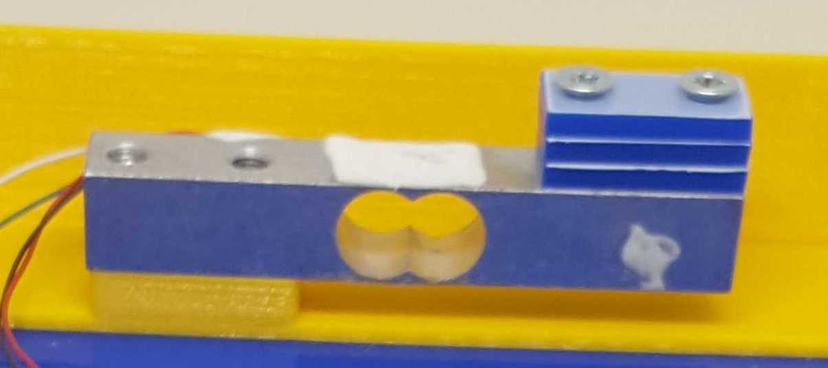
Images/LoadCell.jpg
