Tinamous/ReallySmartBox/Images/Map.jpg

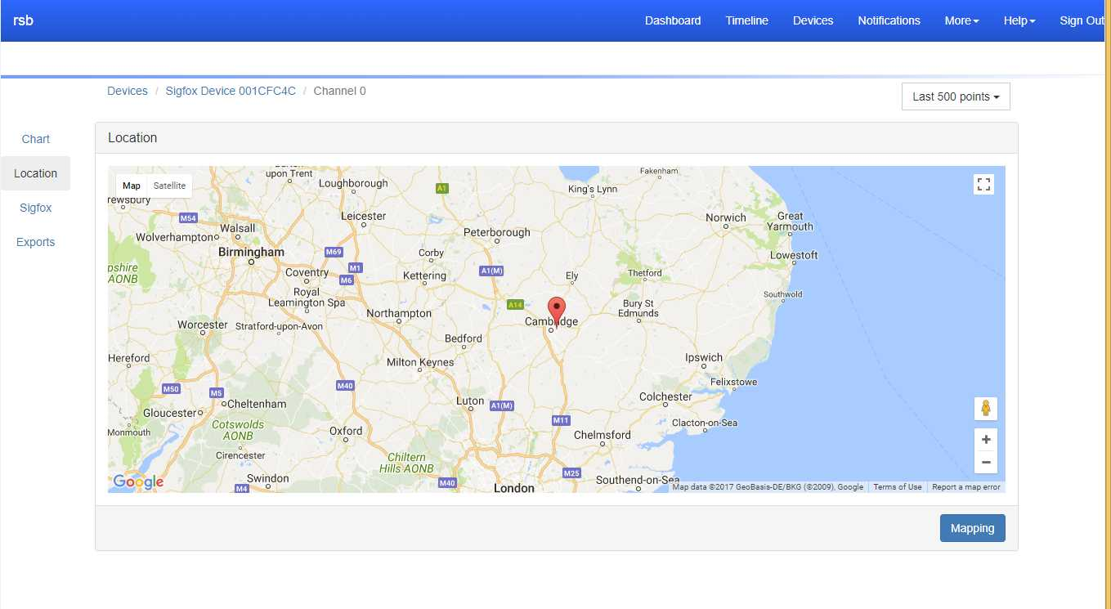
Images/Map.jpg
