Tinamous/ReallySmartBox/Images/Notification1.jpg

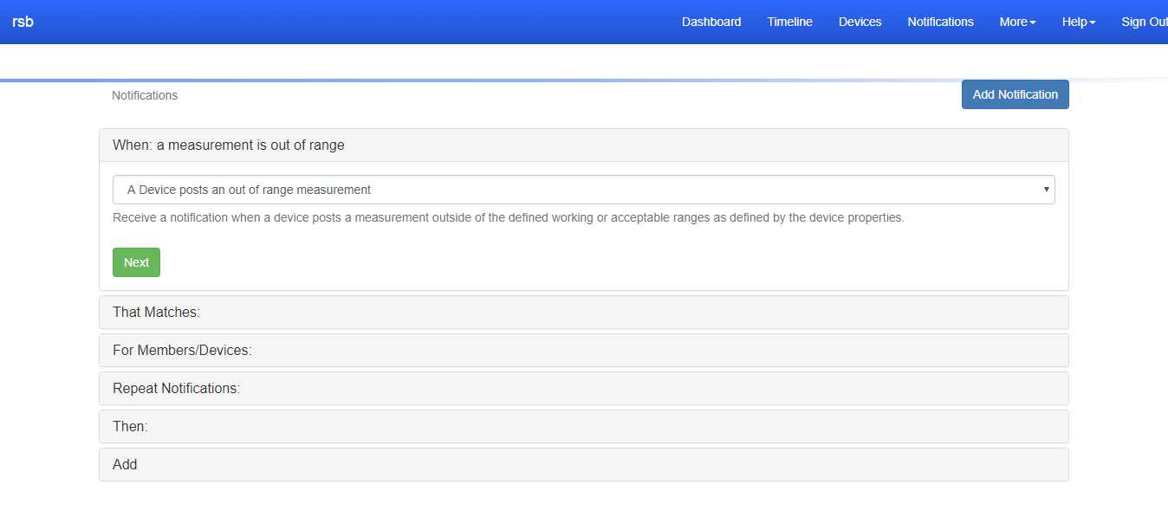
Images/Notification1.jpg
