Tinamous/ReallySmartBox/Images/Notification4.jpg

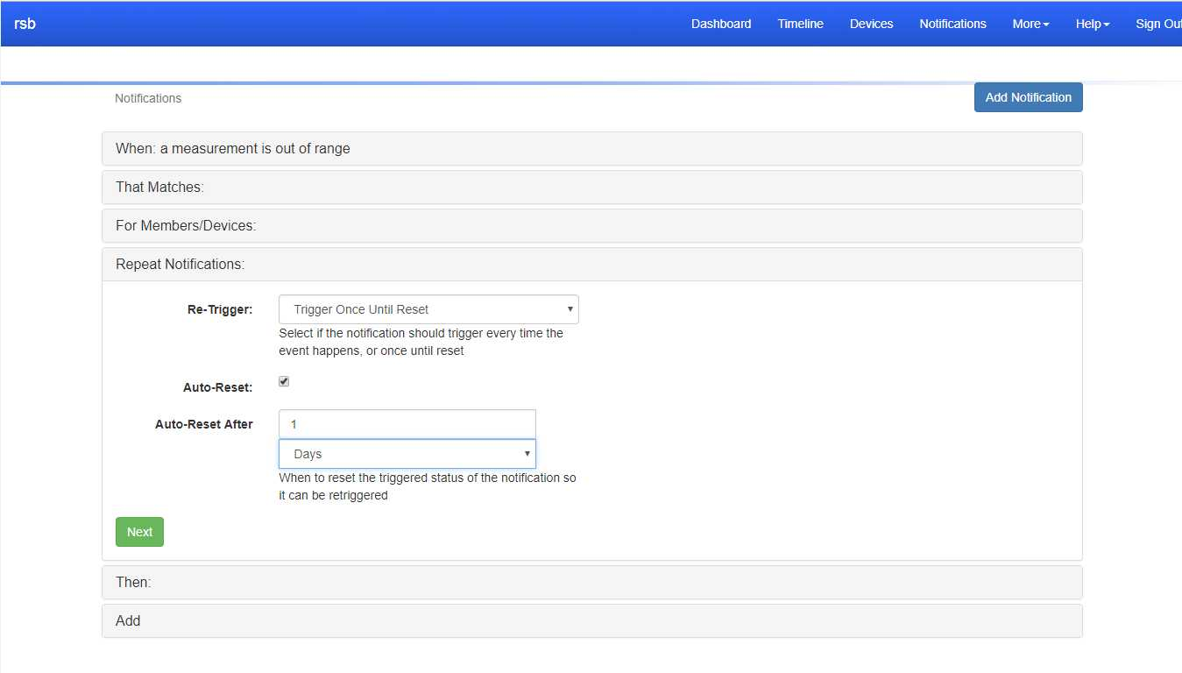
Images/Notification4.jpg
