Tinamous/ReallySmartBox/Images/Notification5.jpg

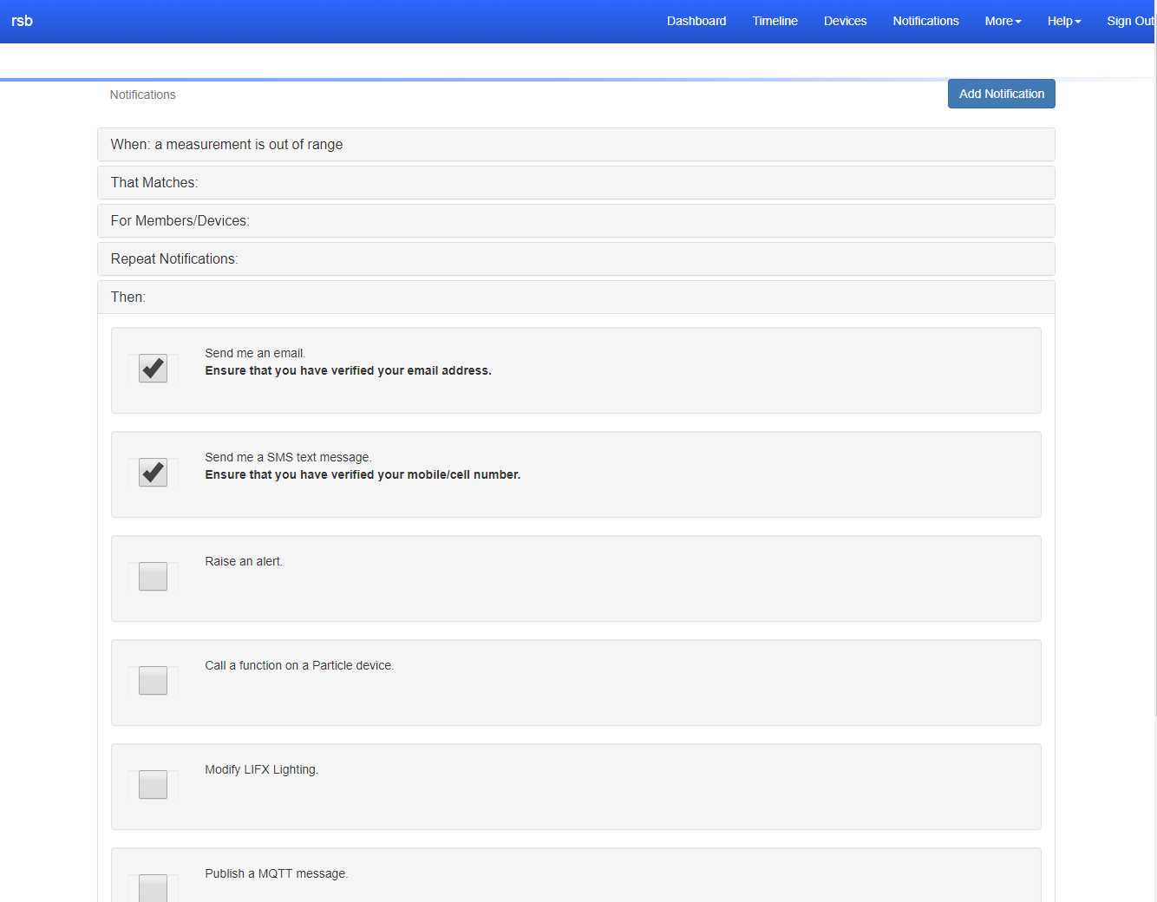
Images/Notification5.jpg
