Tinamous/ReallySmartBox/Images/Notification6.jpg

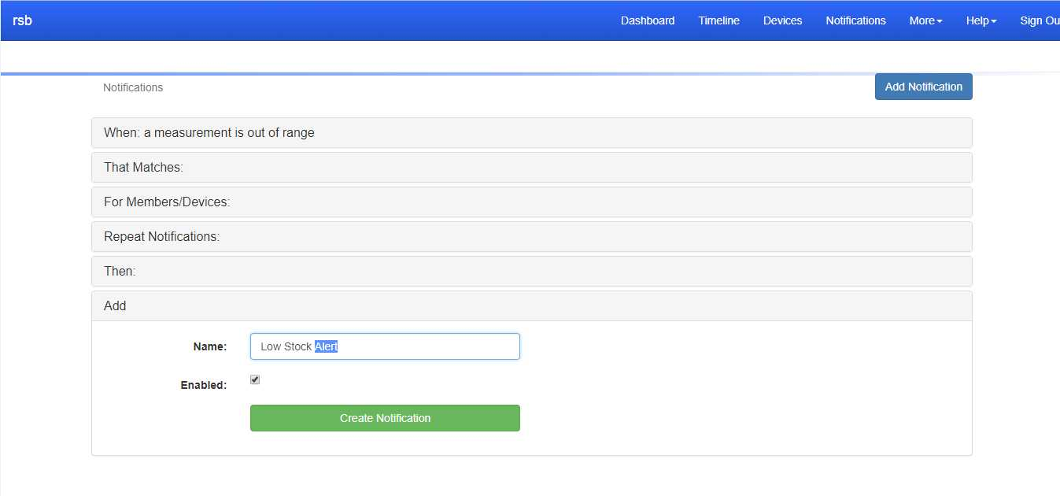
Images/Notification6.jpg
