Tinamous/ReallySmartBox/Images/Notification7.jpg

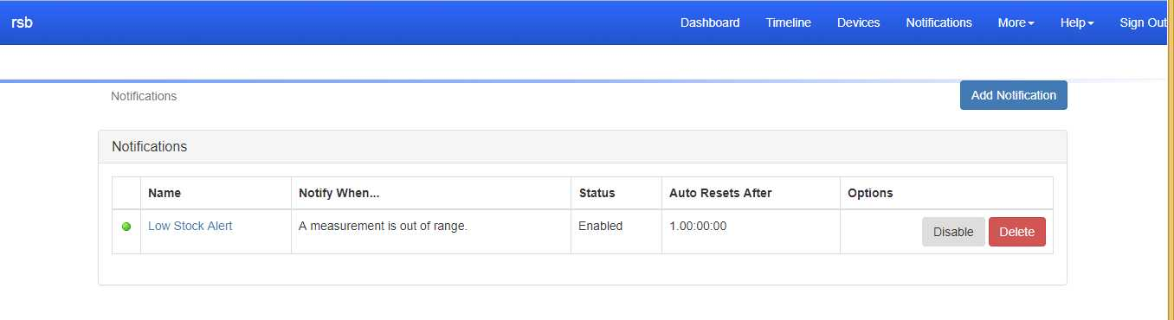
Images/Notification7.jpg
