Tinamous/ReallySmartBox/Images/Unit.jpg

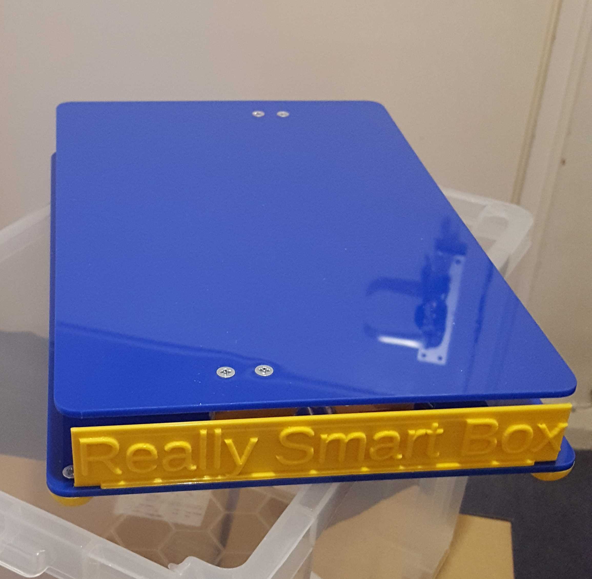
Images/Unit.jpg
