Tinamous/ReallySmartBox/Images/Wiring2.jpg

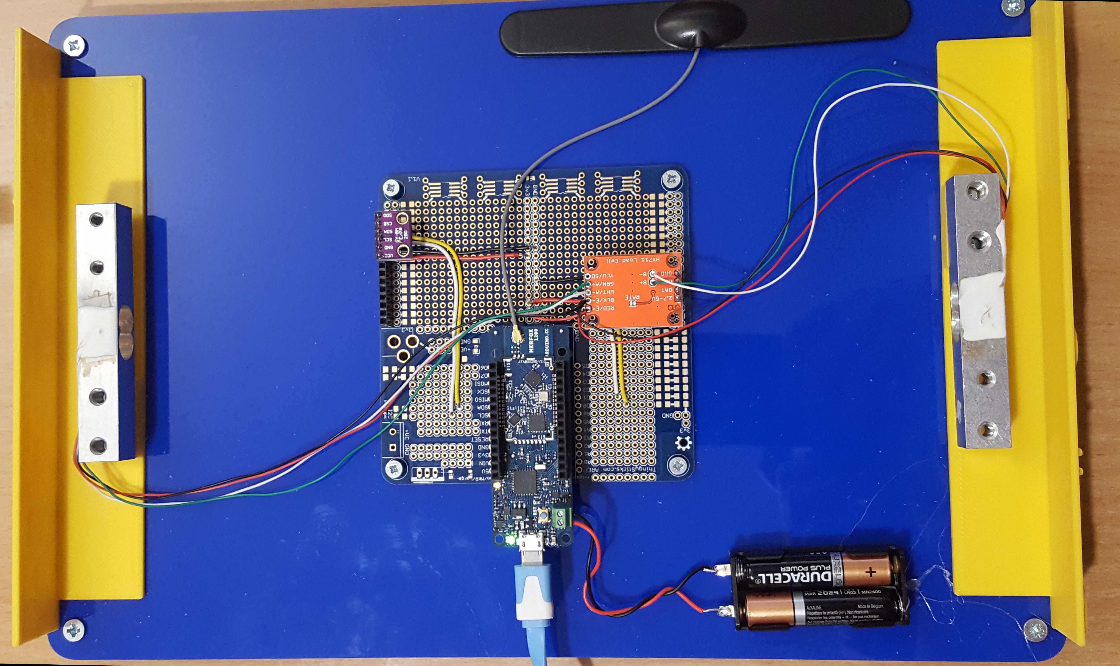
Images/Wiring2.jpg
