Tinamous/ReallySmartBox/Images/Wiring.jpg

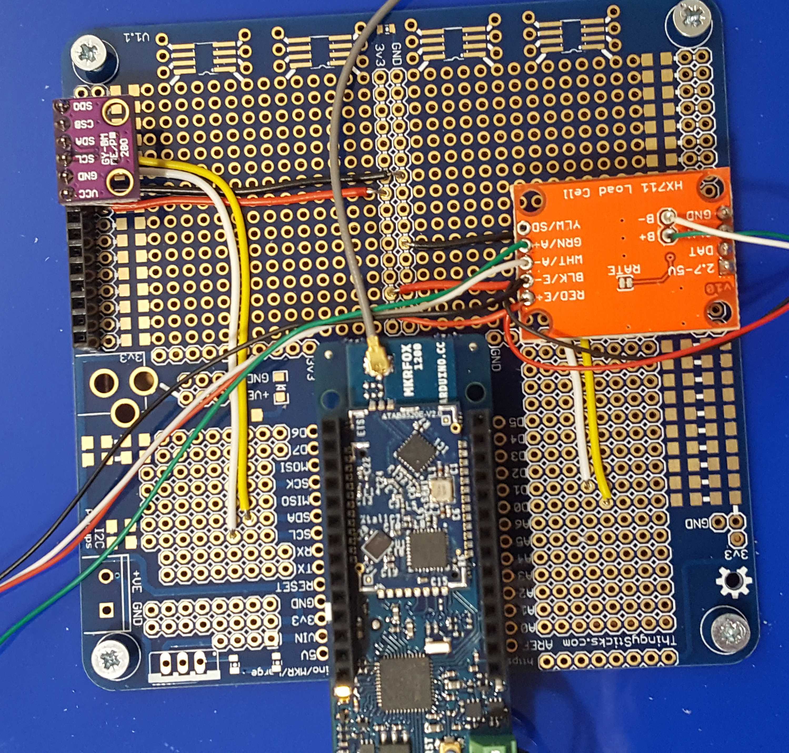
Images/Wiring.jpg
