Tinamous/ReallySmartBox/Images/Calibration2.jpg

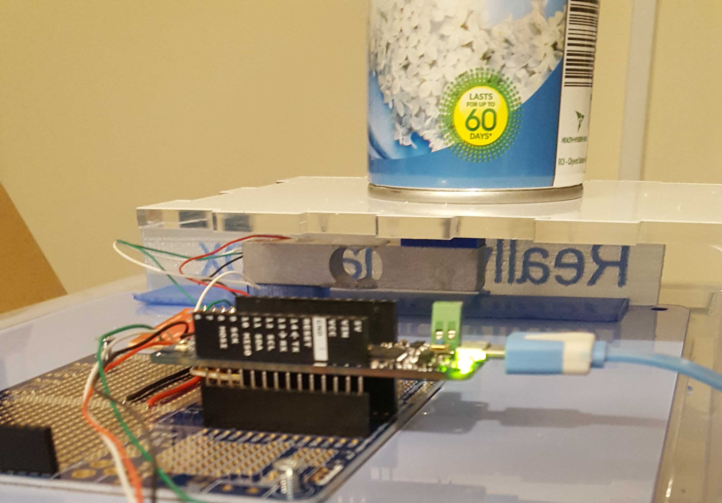
Images/Calibration2.jpg
