Tinamous/ReallySmartBox/Images/Calibration.jpg

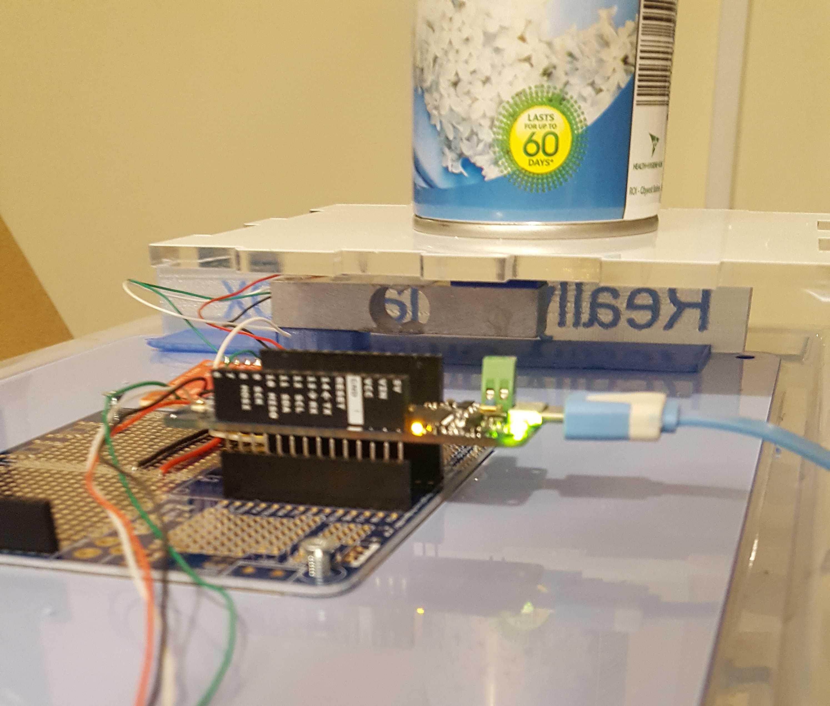
Images/Calibration.jpg
